OpenHisiIpCam/camera-debug-facility/board/hlk-76x8x/module.jpg

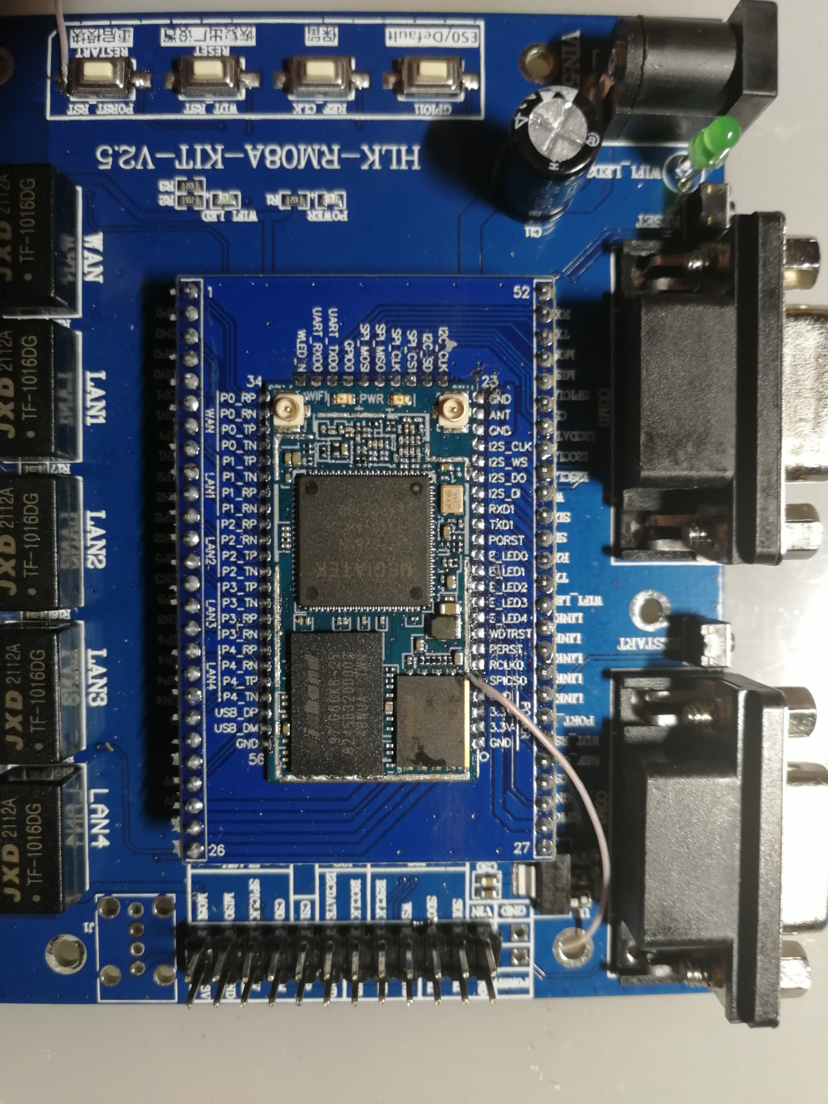
board/hlk-76x8x/module.jpg
