OpenHisiIpCam/camera-debug-facility/board/js7688/drawing.jpg

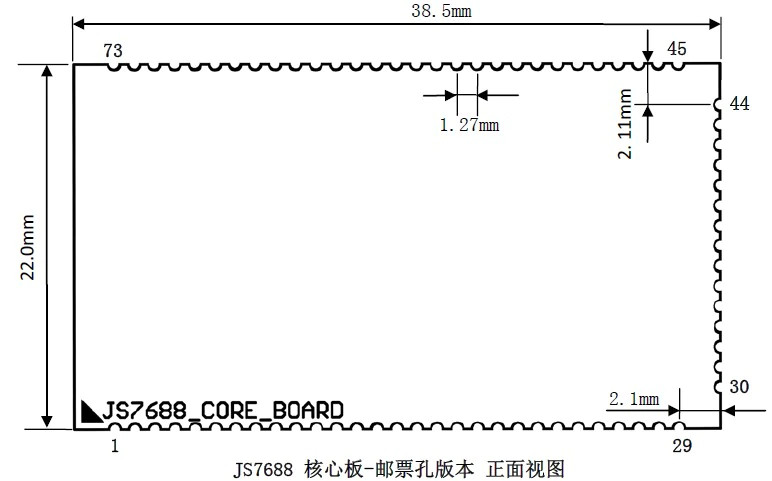
board/js7688/drawing.jpg
