OpenHisiIpCam/camera-debug-facility/board/js7688/js7688.jpg

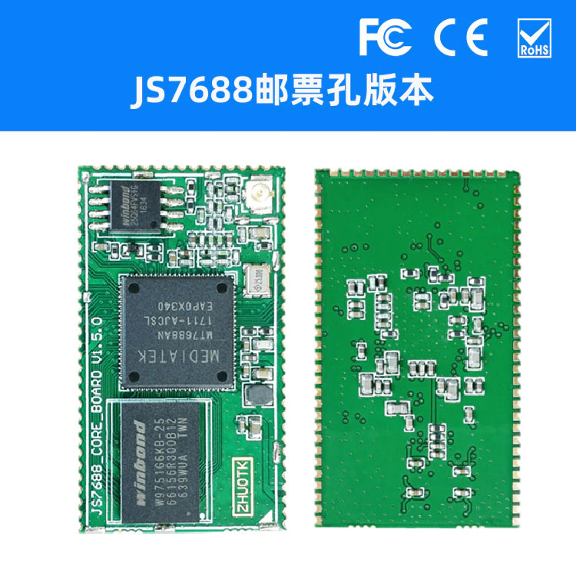
board/js7688/js7688.jpg
