OpenHisiIpCam/camera-debug-facility/hardware/cdf-1/cdf-1-front.jpg

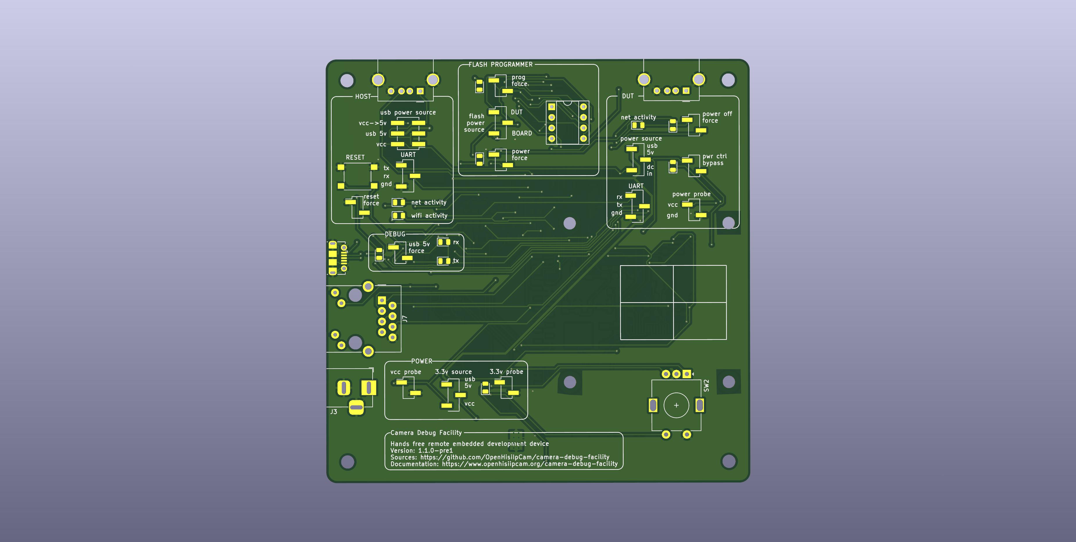
hardware/cdf-1/cdf-1-front.jpg
