OpenHisiIpCam/camera-debug-facility/hardware/references/ssd1306.png

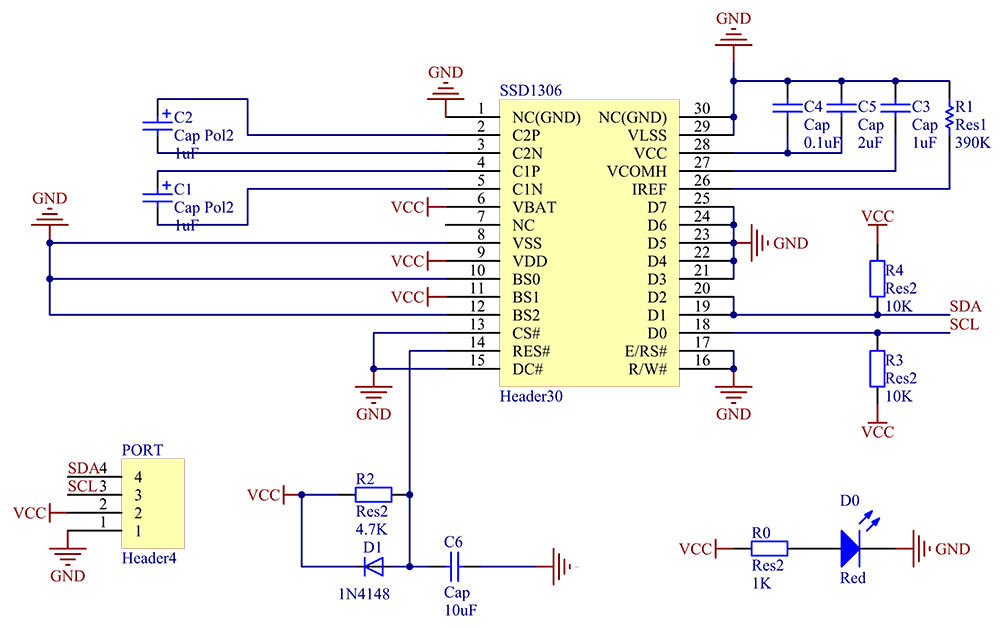
hardware/references/ssd1306.png
