OpenHisiIpCam/camera-debug-facility/board/skw92/skw92a-schematics.pdf

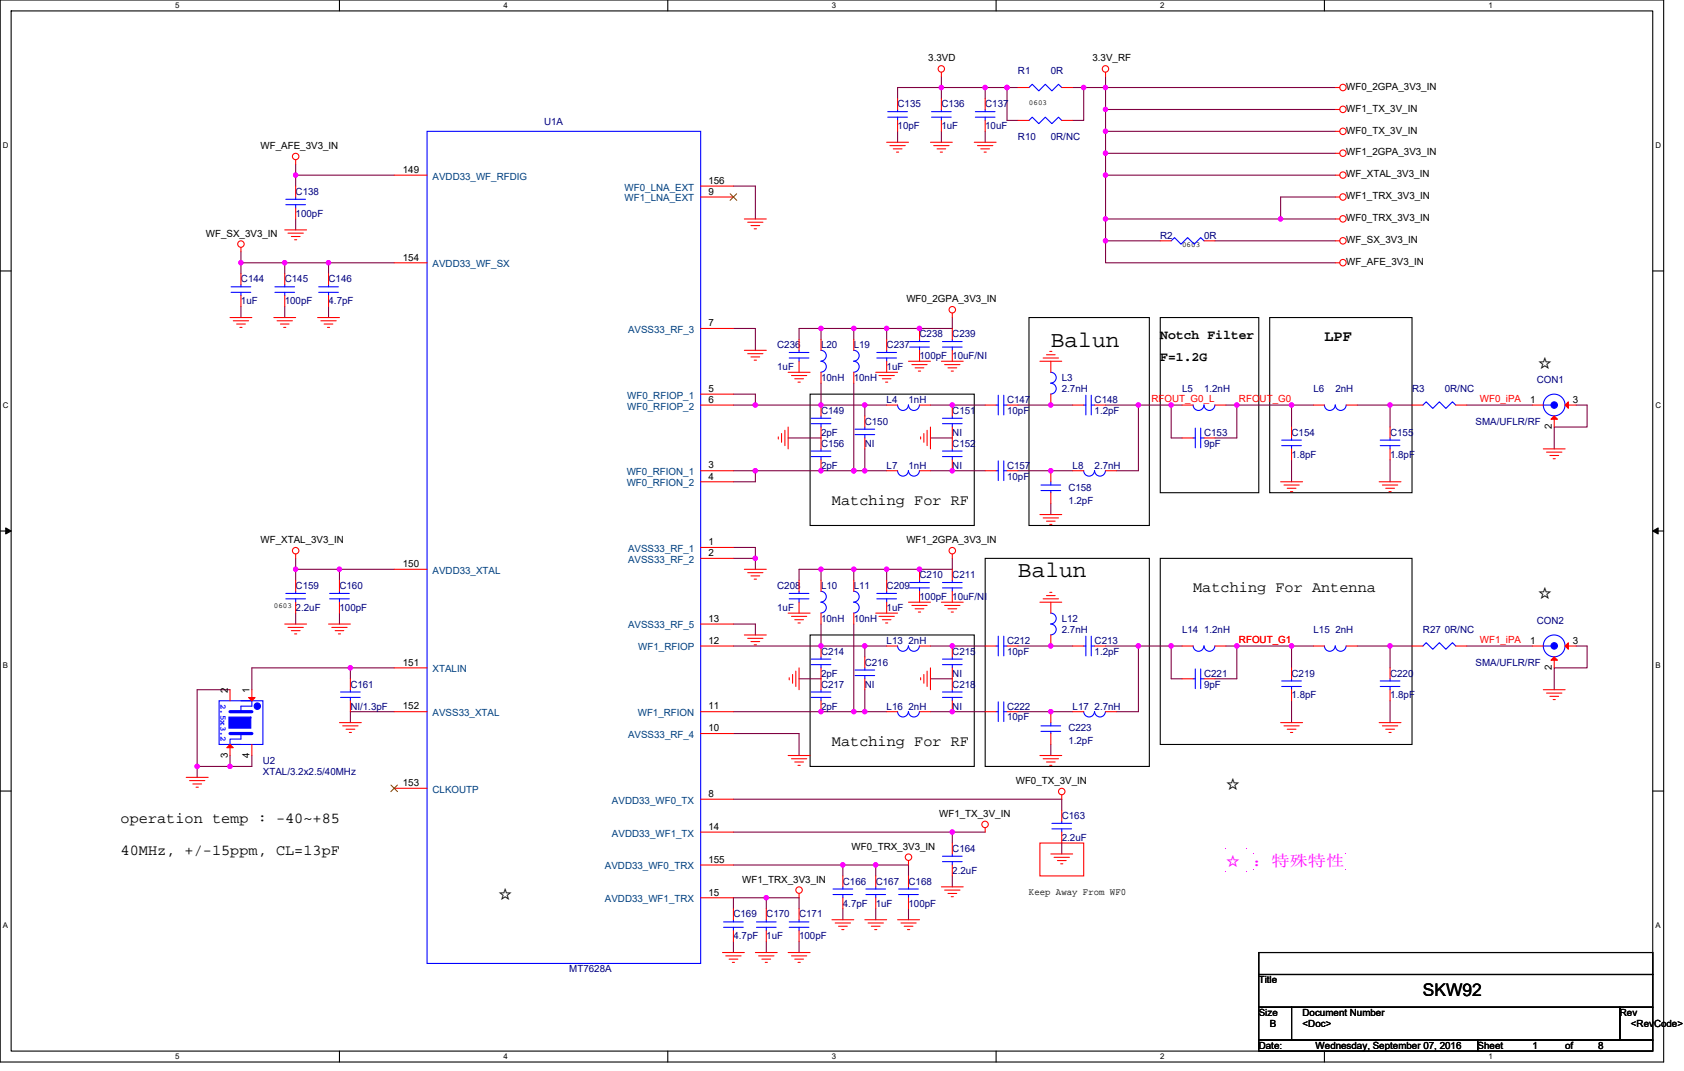
[picture p67: page 1]

CLKOUTP 153 | C223

Matching For RF

Size Size Size B B B | Document Number Document Number Document Number | Rev Rev Rev

Date: Date: Date: Wednesday, September 07, 2016 Wednesday, September 07, 2016 Wednesday, September 07, 2016 | Sheet Sheet Sheet 1 1 1 of of of 8 8 8

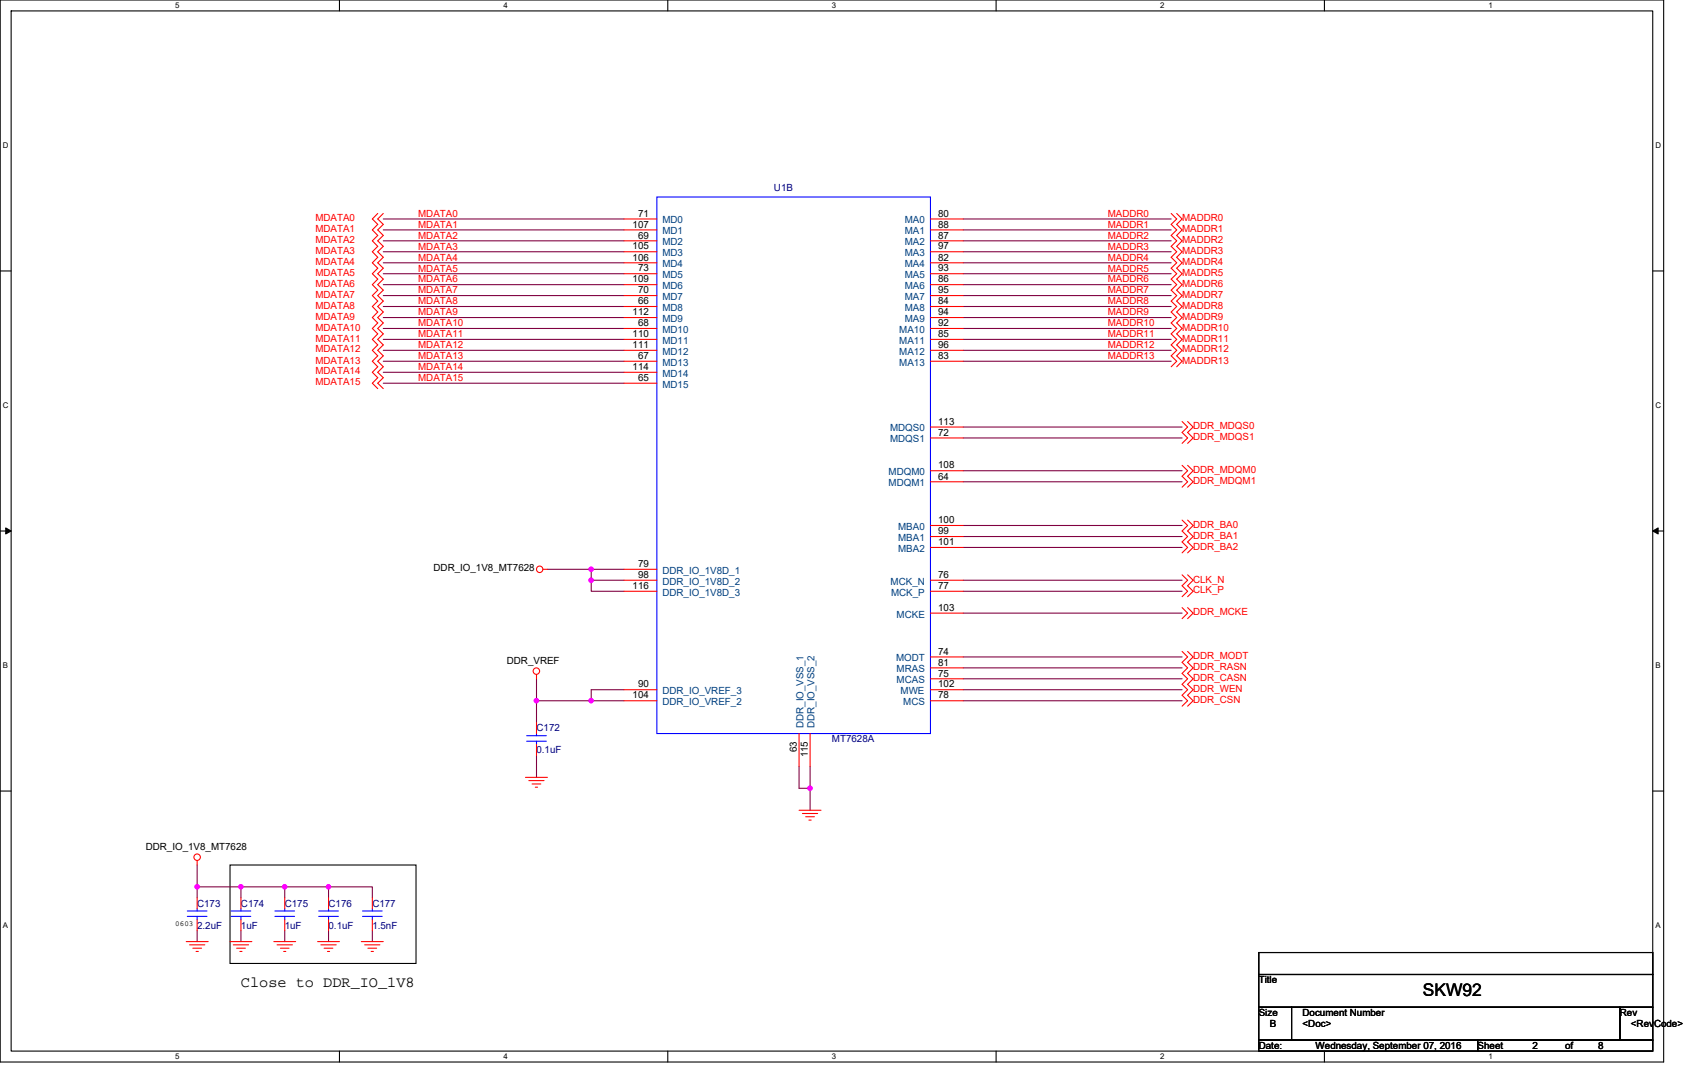
[picture p68: page 2]
Close to DDR_IO_1V8; MADDR0 MADDR1 MADDR2 MADDR3 MADDR4 MADDR5 MADDR6 MADDR7 MADDR8 MADDR9 MADDR10 MADDR11 MADDR12 MADDR13; MDATA0 MDATA1 MDATA2 MDATA3 MDATA4 MDATA5 MDATA6 MDATA7 MDATA8 MDATA9 MDATA10 MDATA11 MDATA12 MDATA13 MDATA14 MDATA15; DDR_IO_1V8_MT7628; DDR_VREF; DDR_MDQS0 DDR_MDQS1; DDR_MDQM0 DDR_MDQM1; DDR_BA0 DDR_BA1 DDR_BA2; CLK_N CLK_P; DDR_MCKE; DDR_MODT DDR_RASN DDR_CASN DDR_WEN DDR_CSN; Title; <Doc>; <RevCode>; SKW92; MDQS0; MDQS1; MDQM0; MDQM1; MBA0; MBA1; MBA2; MCK_N; MCK_P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

Size Size Size B B B | Document Number Document Number Document Number | Rev Rev Rev

Date: Date: Date: Wednesday, September 07, 2016 Wednesday, September 07, 2016 Wednesday, September 07, 2016 | Sheet Sheet Sheet 2 2 2 of of of 8 8 8

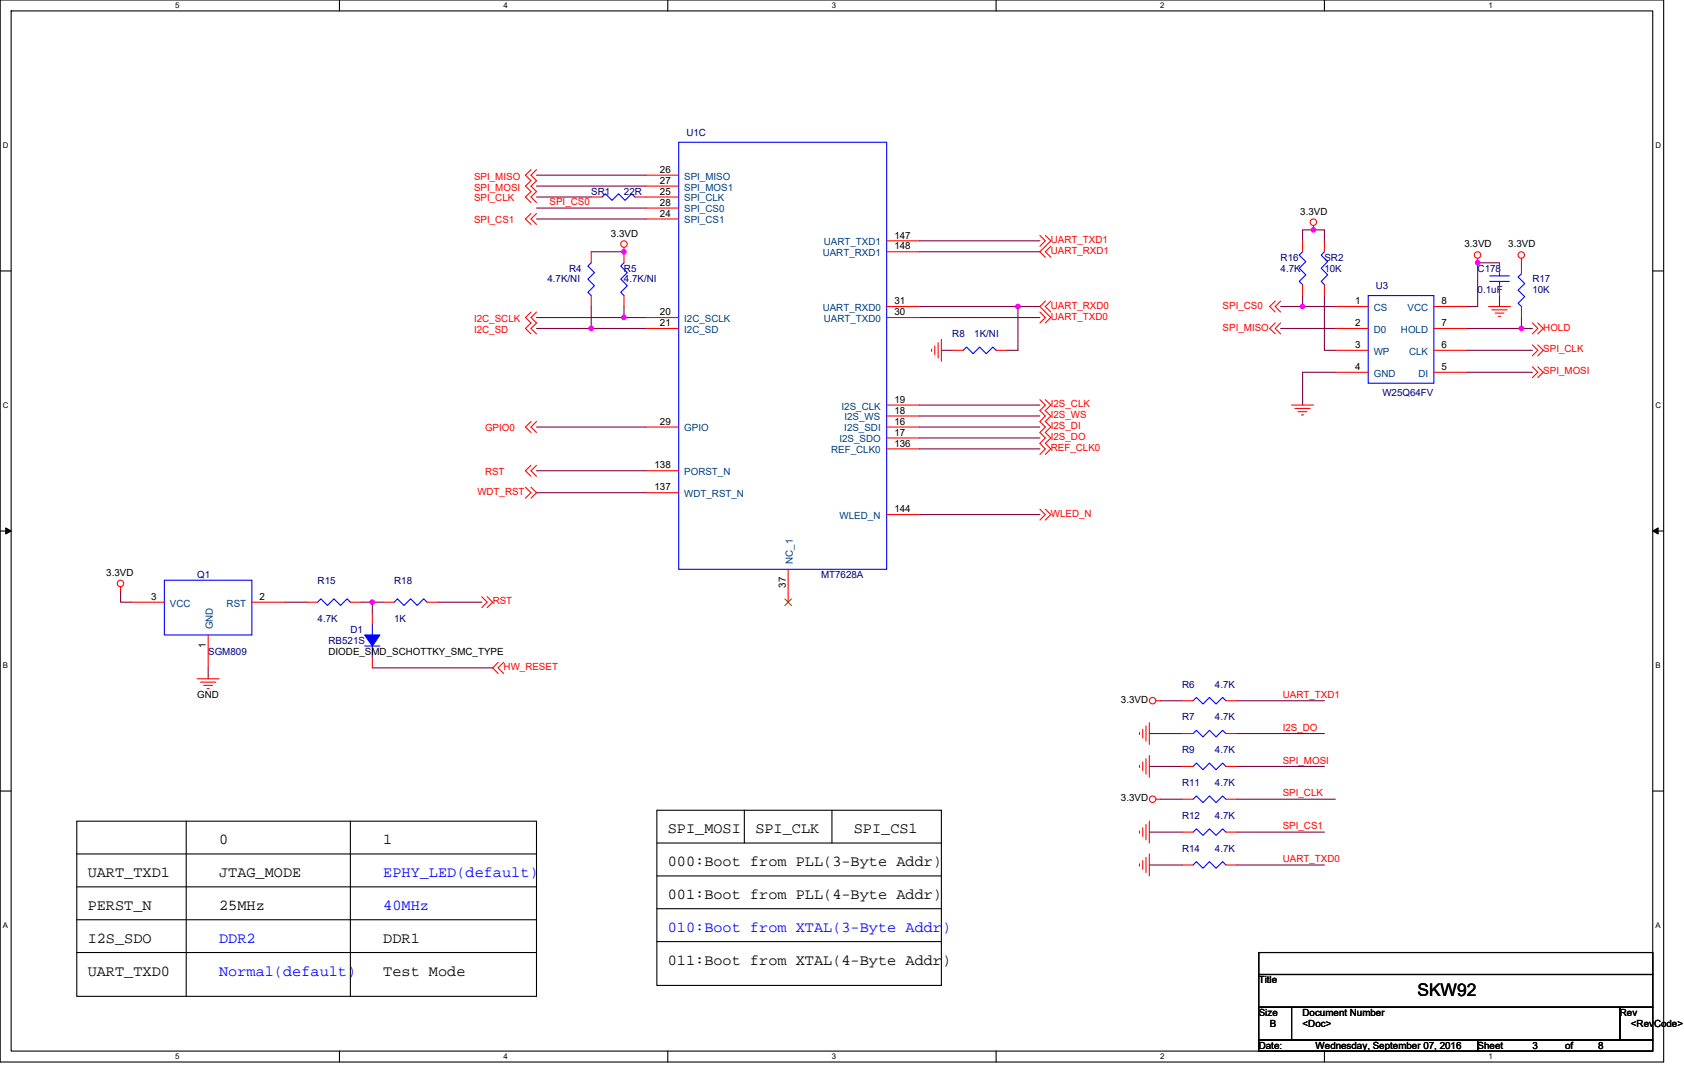
[picture p69: page 3]

000:Boot from PLL(3-Byte Addr)

UART_TXD1 | JTAG_MODE | EPHY_LED(default)

001:Boot from PLL(4-Byte Addr)

PERST_N | 25MHz | 40MHz

010:Boot from XTAL(3-Byte Addr)

I2S_SDO | DDR2 | DDR1

011:Boot from XTAL(4-Byte Addr)

UART_TXD0 | | Test Mode Normal(default)

Size Size Size B B B | Document Number Document Number Document Number | Rev Rev Rev

Date: Date: Date: Wednesday, September 07, 2016 Wednesday, September 07, 2016 Wednesday, September 07, 2016 | Sheet Sheet Sheet 3 3 3 of of of 8 8 8

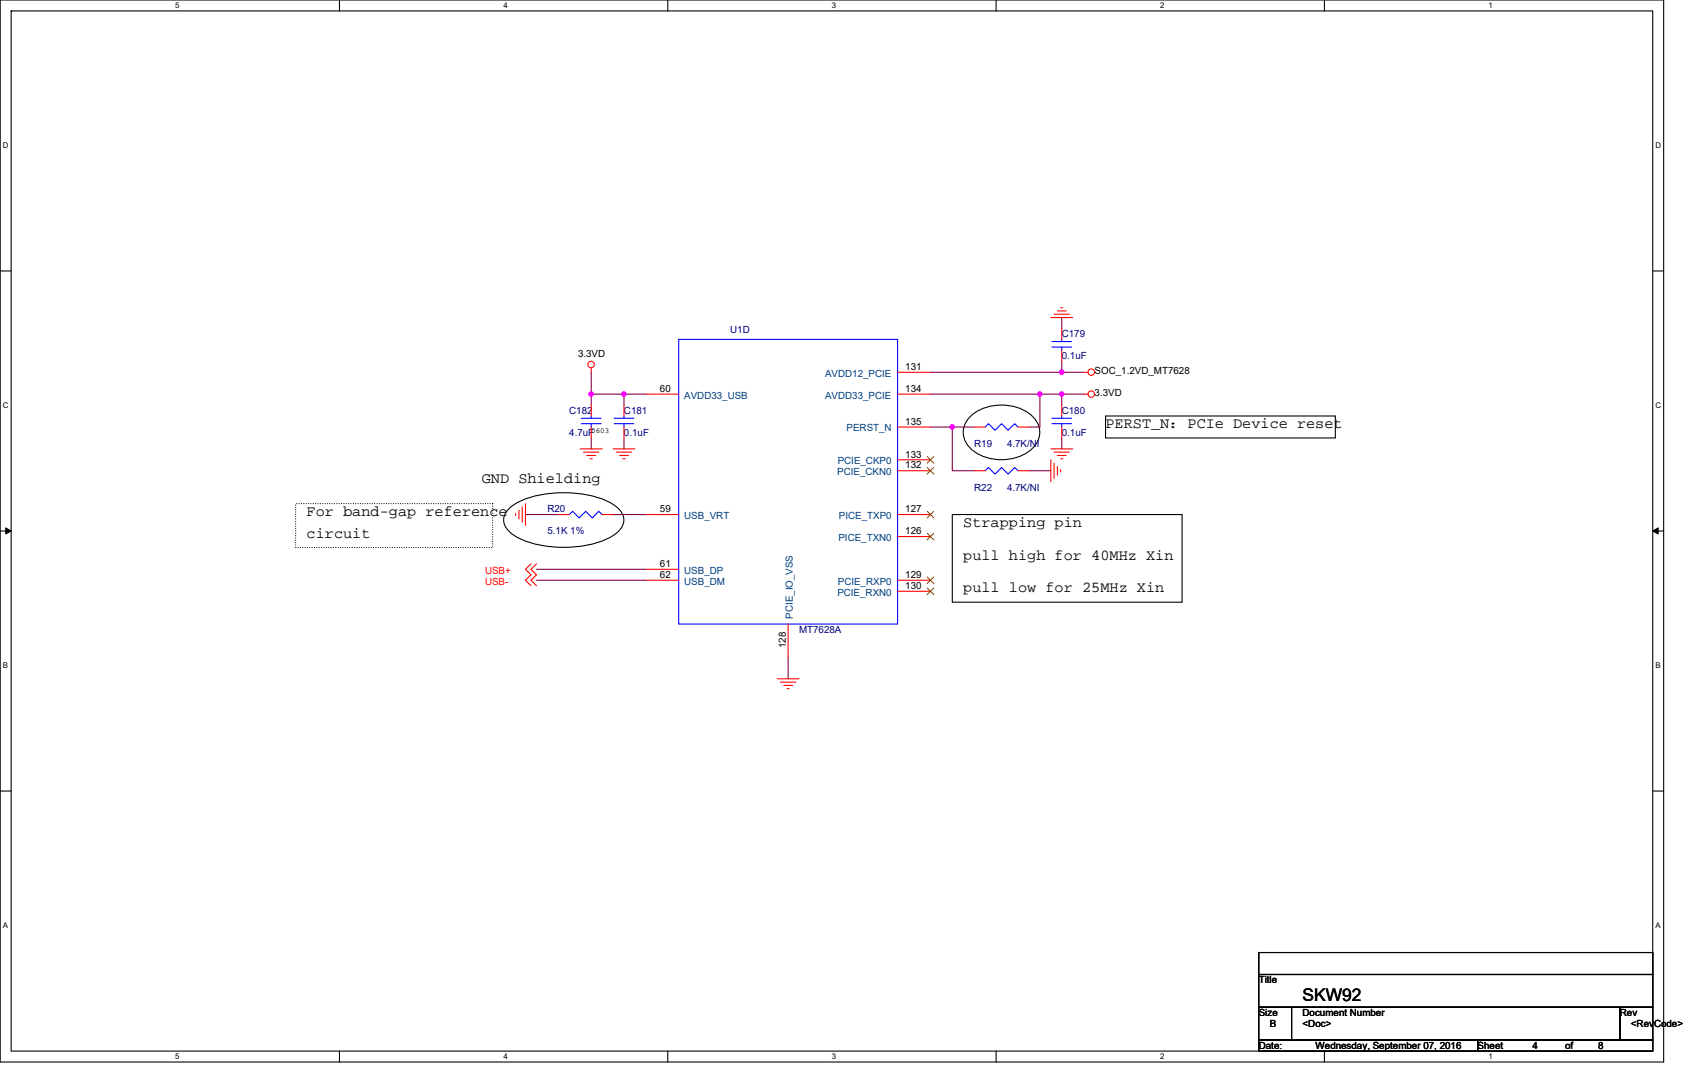
[picture p70: page 4]

For band-gap reference
circuit

pull high for 40MHz Xin

pull low for 25MHz Xin

Size Size Size B B B | Document Number Document Number Document Number | Rev Rev Rev

Date: Date: Date: Wednesday, September 07, 2016 Wednesday, September 07, 2016 Wednesday, September 07, 2016 | Sheet Sheet Sheet 4 4 4 of of of 8 8 8

## Close to MT7628A

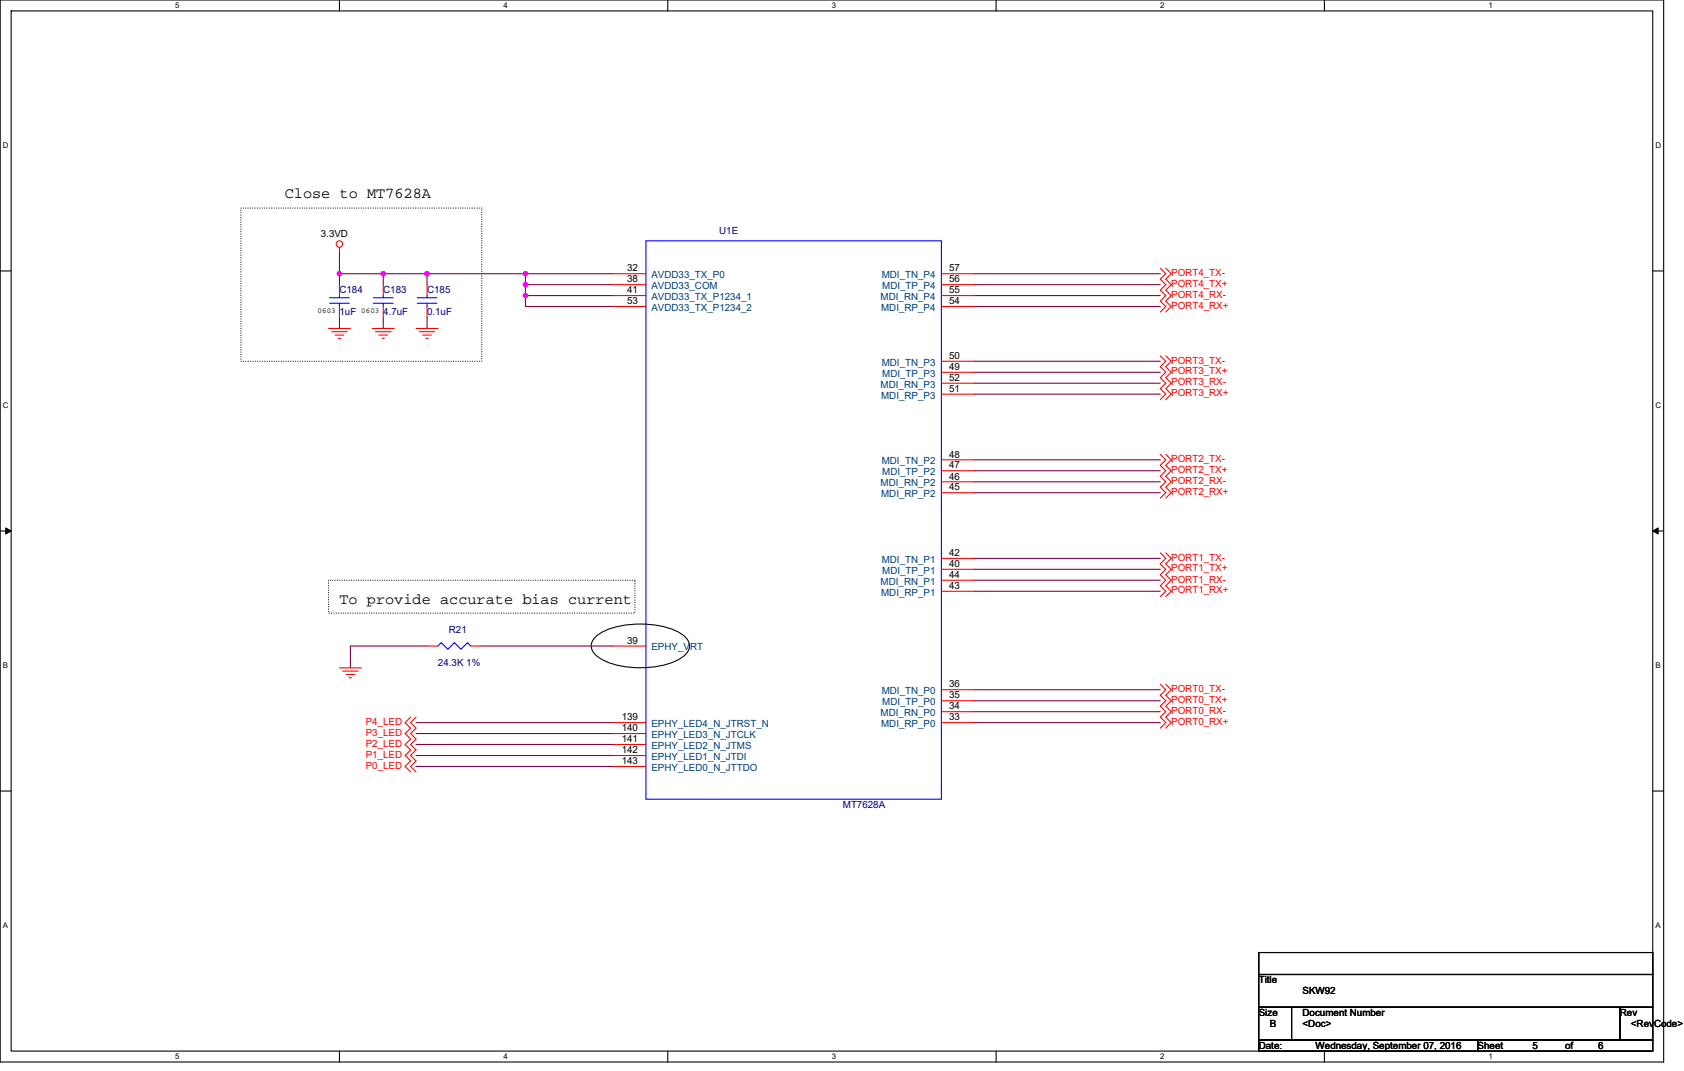
[picture p71: page 5]
PORT0_RX+; PORT0_RX-; PORT0_TX- PORT0_TX+; P4_LED P3_LED P2_LED P1_LED; PORT1_RX+; PORT1_RX-; PORT1_TX- PORT1_TX+; PORT2_RX+; PORT2_RX-; PORT2_TX- PORT2_TX+; PORT3_RX+; PORT3_RX-; PORT3_TX- PORT3_TX+; PORT4_RX+; PORT4_RX-; PORT4_TX- PORT4_TX+; P0_LED; Title; <Doc>; <RevCode>; SKW92; MDI_TN_P4; MDI_TP_P4; MDI_RN_P4; MDI_RP_P4; MDI_TN_P3; MDI_TP_P3; MDI_RN_P3; MDI_RP_P3; MDI_TN_P2; MDI_TP_P2; MDI_RN_P2; MDI_RP_P2; MDI_TN_P1; MDI_TP_P1; MDI_RN_P1; MDI_RP_P1; MDI_TN_P0; MDI_TP_P0; MDI_RN_P0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

To provide accurate bias current

Size Size Size B B B | Document Number Document Number Document Number | Rev Rev Rev

Date: Date: Date: Wednesday, September 07, 2016 Wednesday, September 07, 2016 Wednesday, September 07, 2016 | Sheet Sheet Sheet 5 5 5 of of of 6 6 6

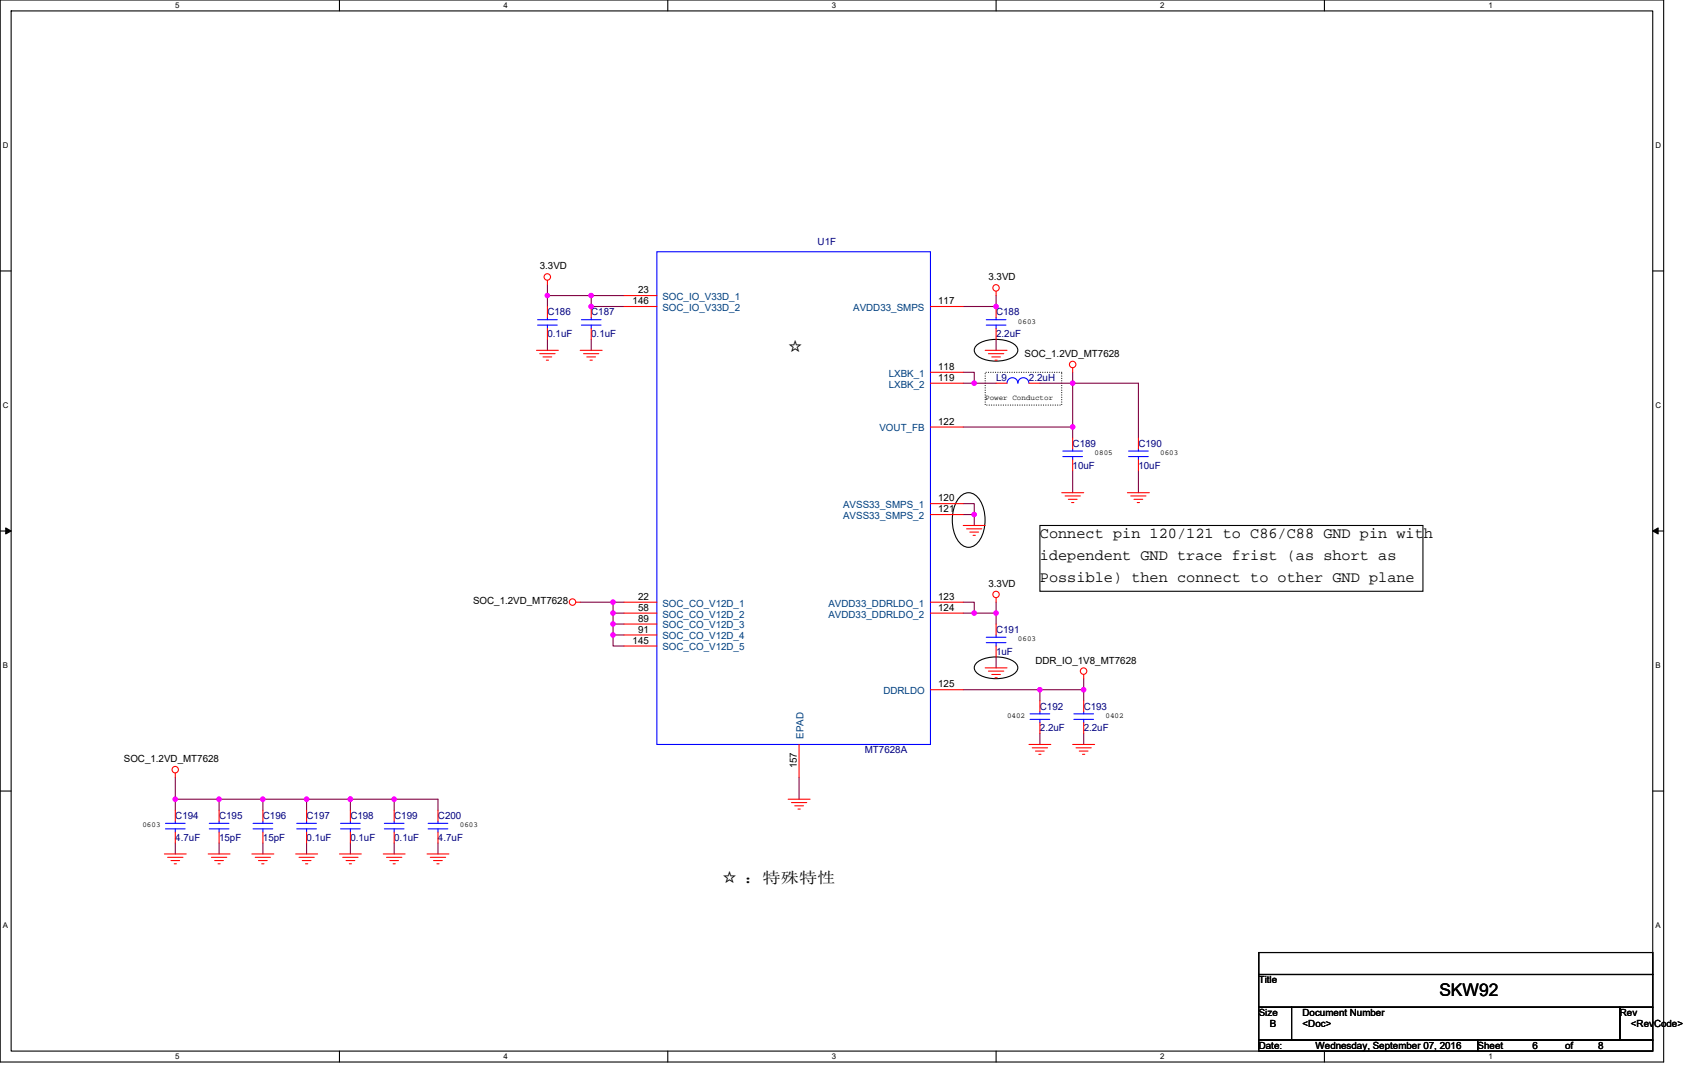
[picture p72: page 6]

Connect pin 120/121 to C86/C88 GND pin with
idependent GND trace frist (as short as
Possible) then connect to other GND plane

Size Size Size B B B | Document Number Document Number Document Number | Rev Rev Rev

Date: Date: Date: Wednesday, September 07, 2016 Wednesday, September 07, 2016 Wednesday, September 07, 2016 | Sheet Sheet Sheet 6 6 6 of of of 8 8 8

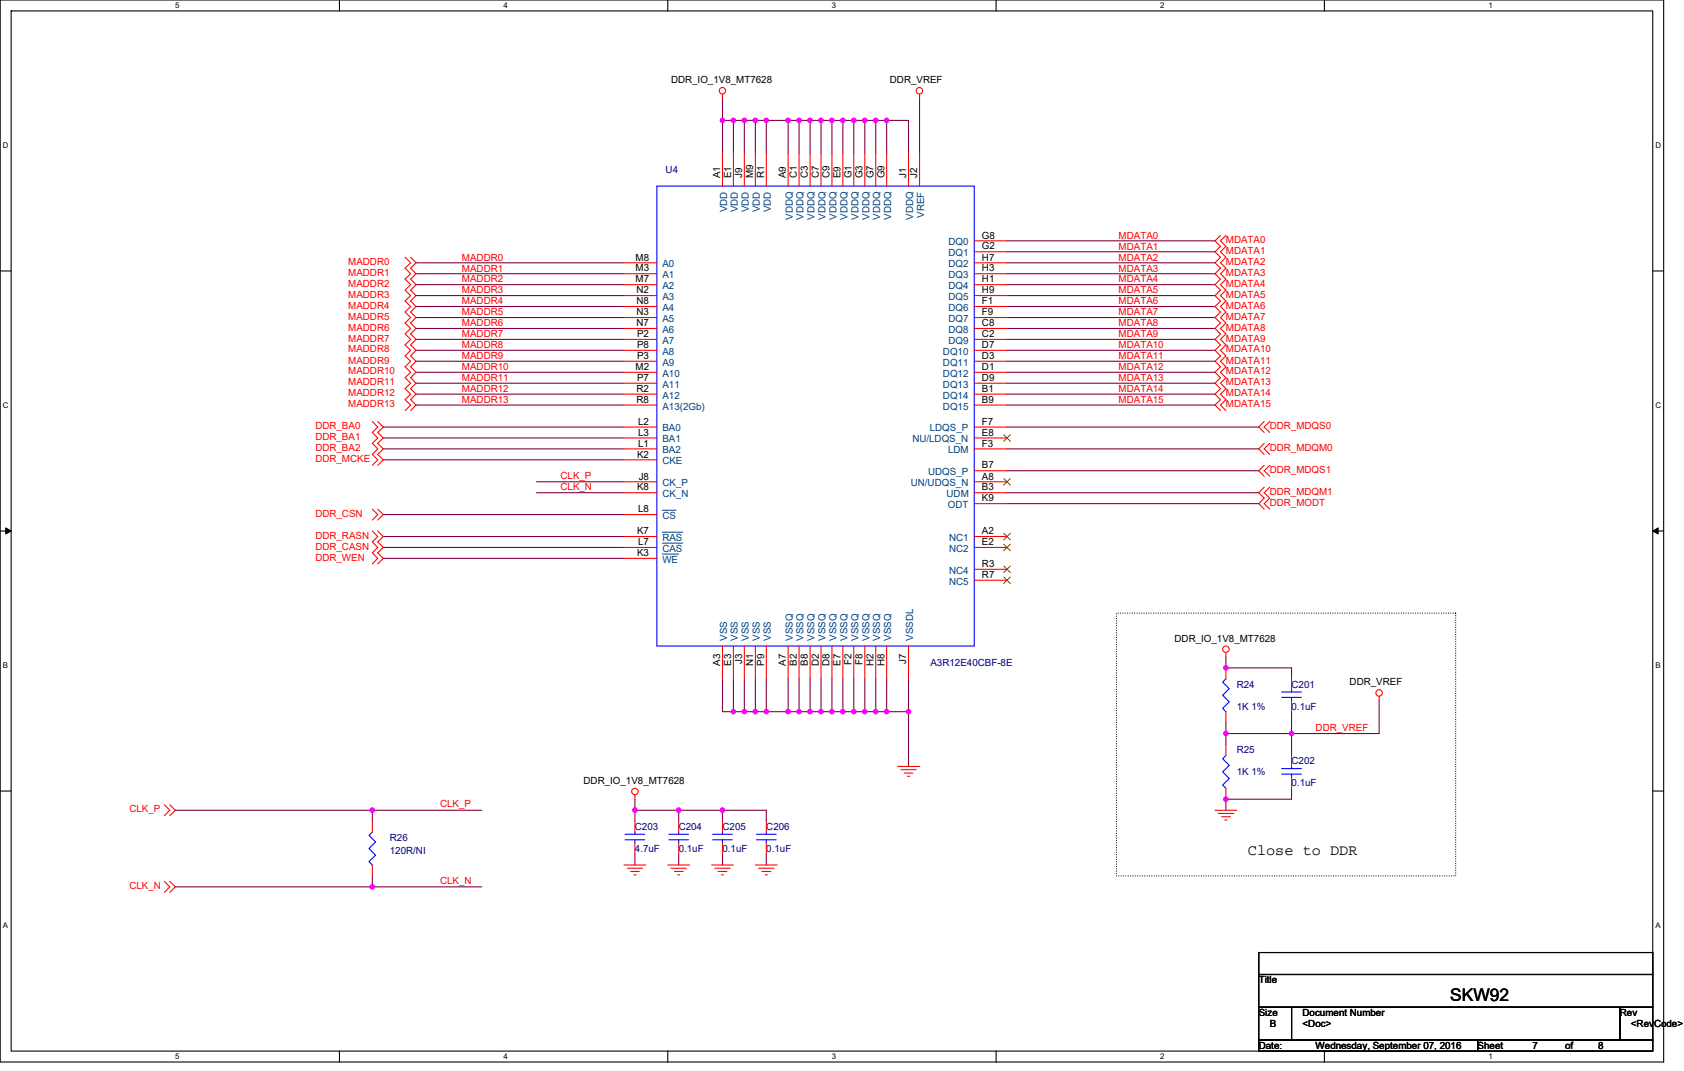
[picture p73: page 7]

Size Size Size B B B | Document Number Document Number Document Number | Rev Rev Rev

Date: Date: Date: Wednesday, September 07, 2016 Wednesday, September 07, 2016 Wednesday, September 07, 2016 | Sheet Sheet Sheet 7 7 7 of of of 8 8 8

## Port3 and port4 multiplexing

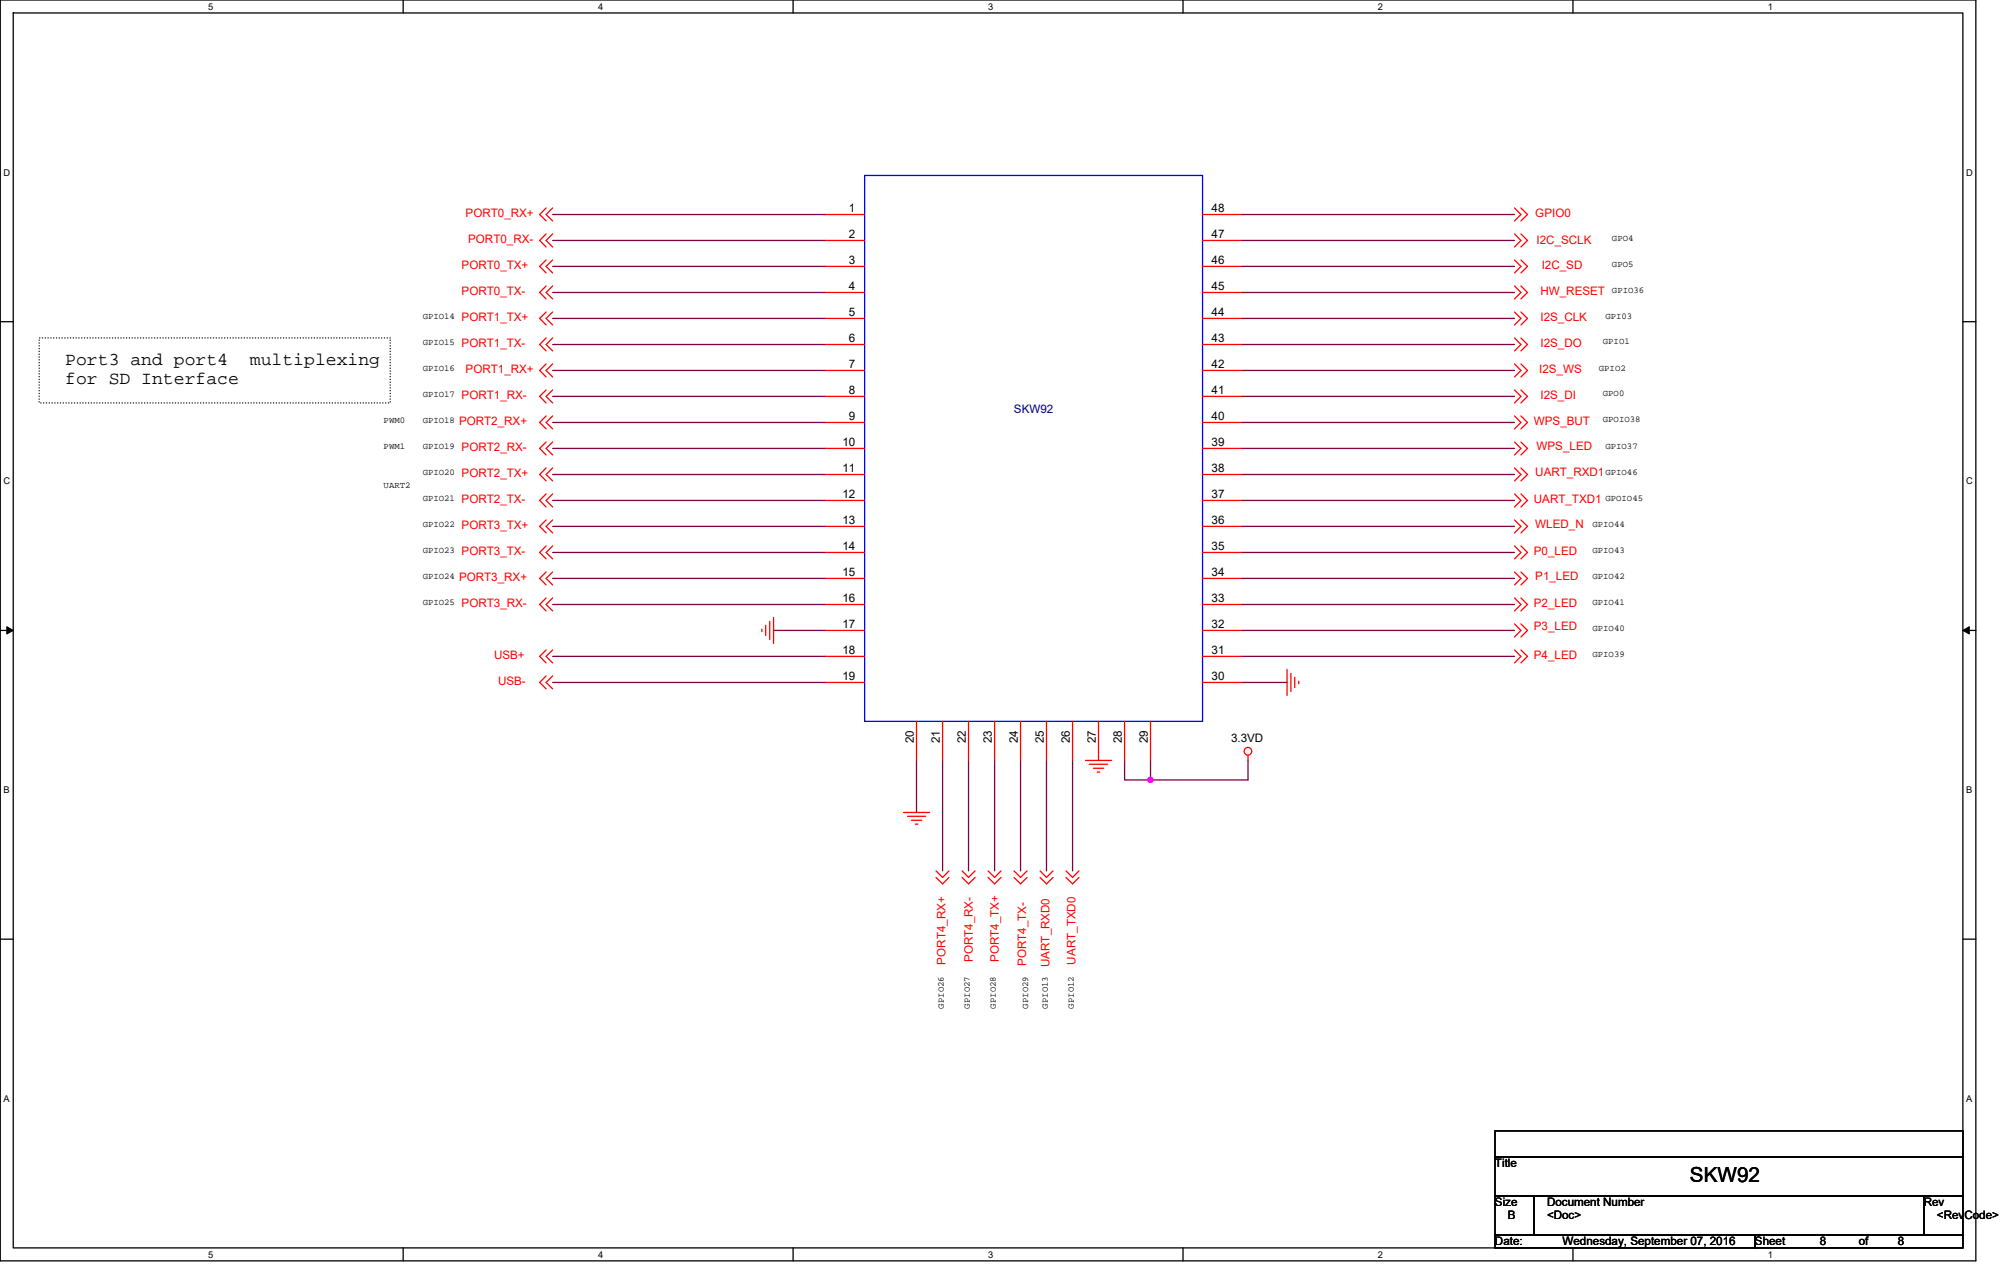
[picture p74: page 8]
PWM1; PWM0; GPI03; GPIO2; GPIO1; GPO0; GPIO13; GPIO12; GPIO21; GPIO22; GPIO23; GPIO24; GPIO25; GPIO18; GPIO17; GPIO16; GPIO15; GPIO14; GPIO20; GPIO19; UART2; GPIO26; GPIO27; GPIO28; GPIO29; GPIO46; GPOIO45; GPIO44; GPIO42; GPIO43; GPO5; GPO4; GPIO37; GPIO41; GPIO40; GPIO39; GPOIO38; GPIO36; PORT1_TX+; PORT1_RX+; PORT1_RX-; PORT1_TX-; PORT2_RX+; PORT2_RX-; PORT2_TX+; PORT2_TX-; PORT3_TX+; PORT3_TX-; PORT3_RX+; PORT3_RX-; PORT0_RX+ PORT0_RX- PORT0_TX+ PORT0_TX-; PORT4_RX+; PORT4_RX-; PORT4_TX+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

for SD Interface

Size Size Size B B B | Document Number Document Number Document Number | Rev Rev Rev

Date: Date: Date: Wednesday, September 07, 2016 Wednesday, September 07, 2016 Wednesday, September 07, 2016 | Sheet Sheet Sheet 8 8 8 of of of 8 8 8
