OpenHisiIpCam/camera-debug-facility/board/js7688/JS76x8_base_board_sch_v1.7.2.pdf

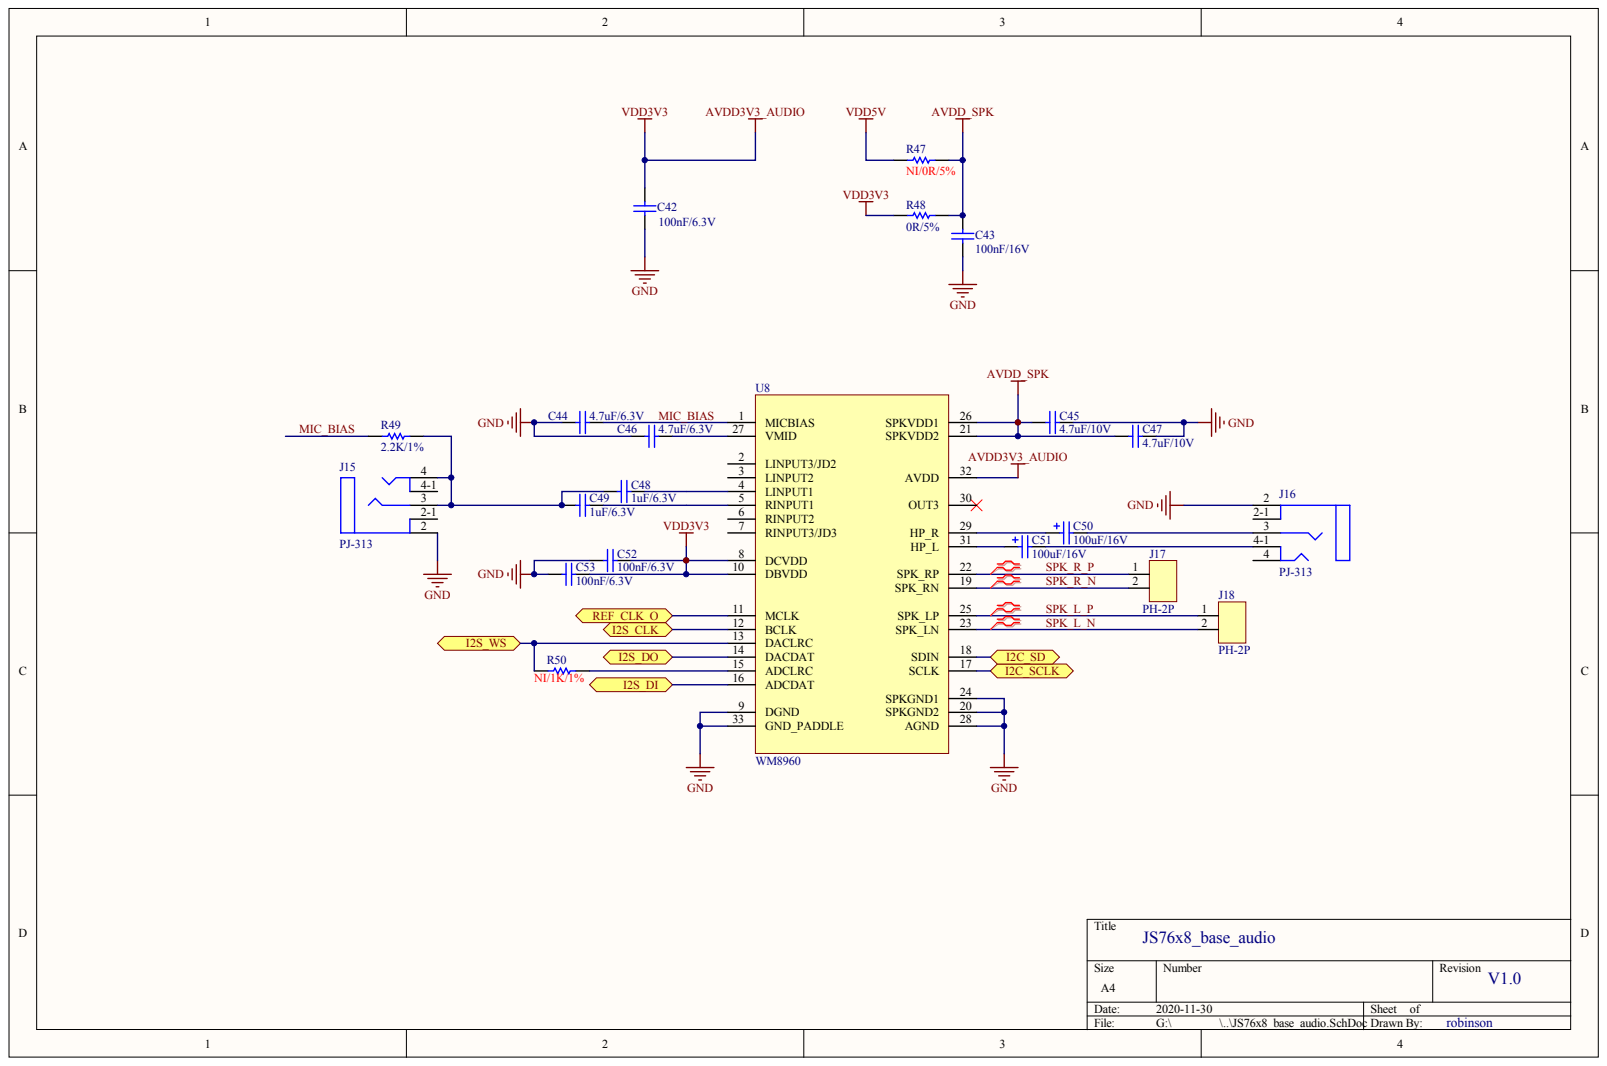
[picture p75: page 1]

VMID 27 | 4.7uF/10V | C47

4 | LINPUT3/JD2 2

C53 | | 100nF/6.3V | DBVDD 10

MCLK 11 BCLK 12 DACLRC 13 | SPK_R_N 2

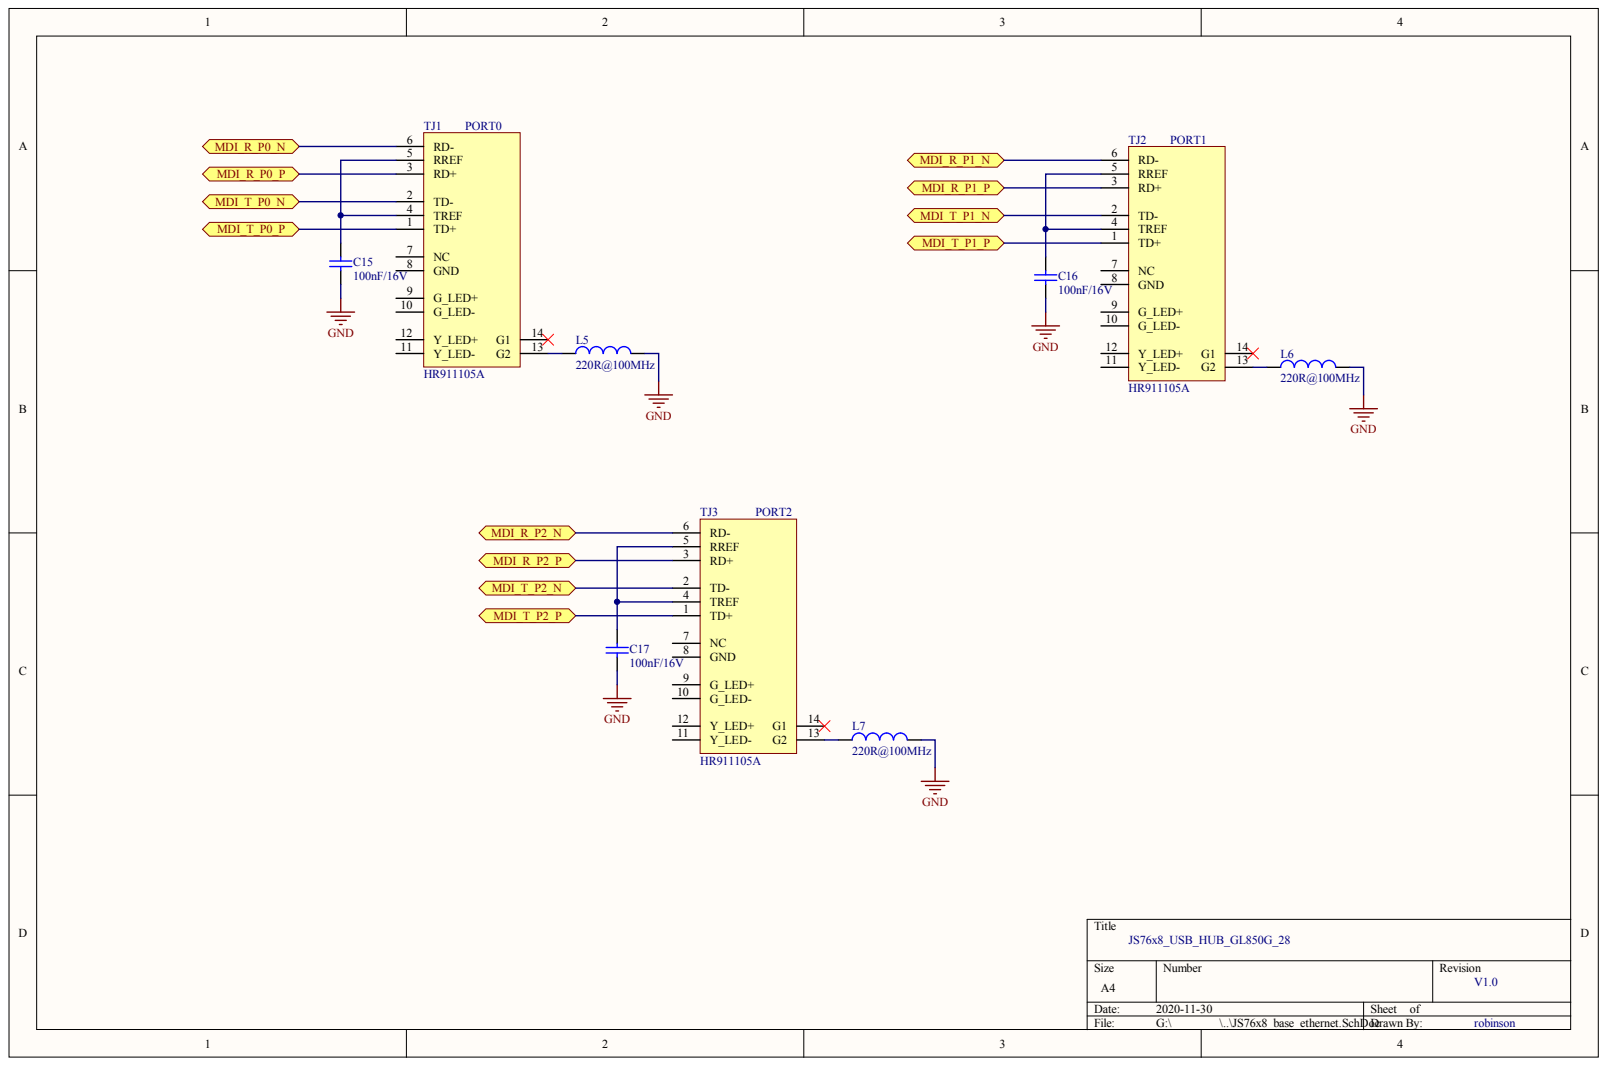
[picture p76: page 2]

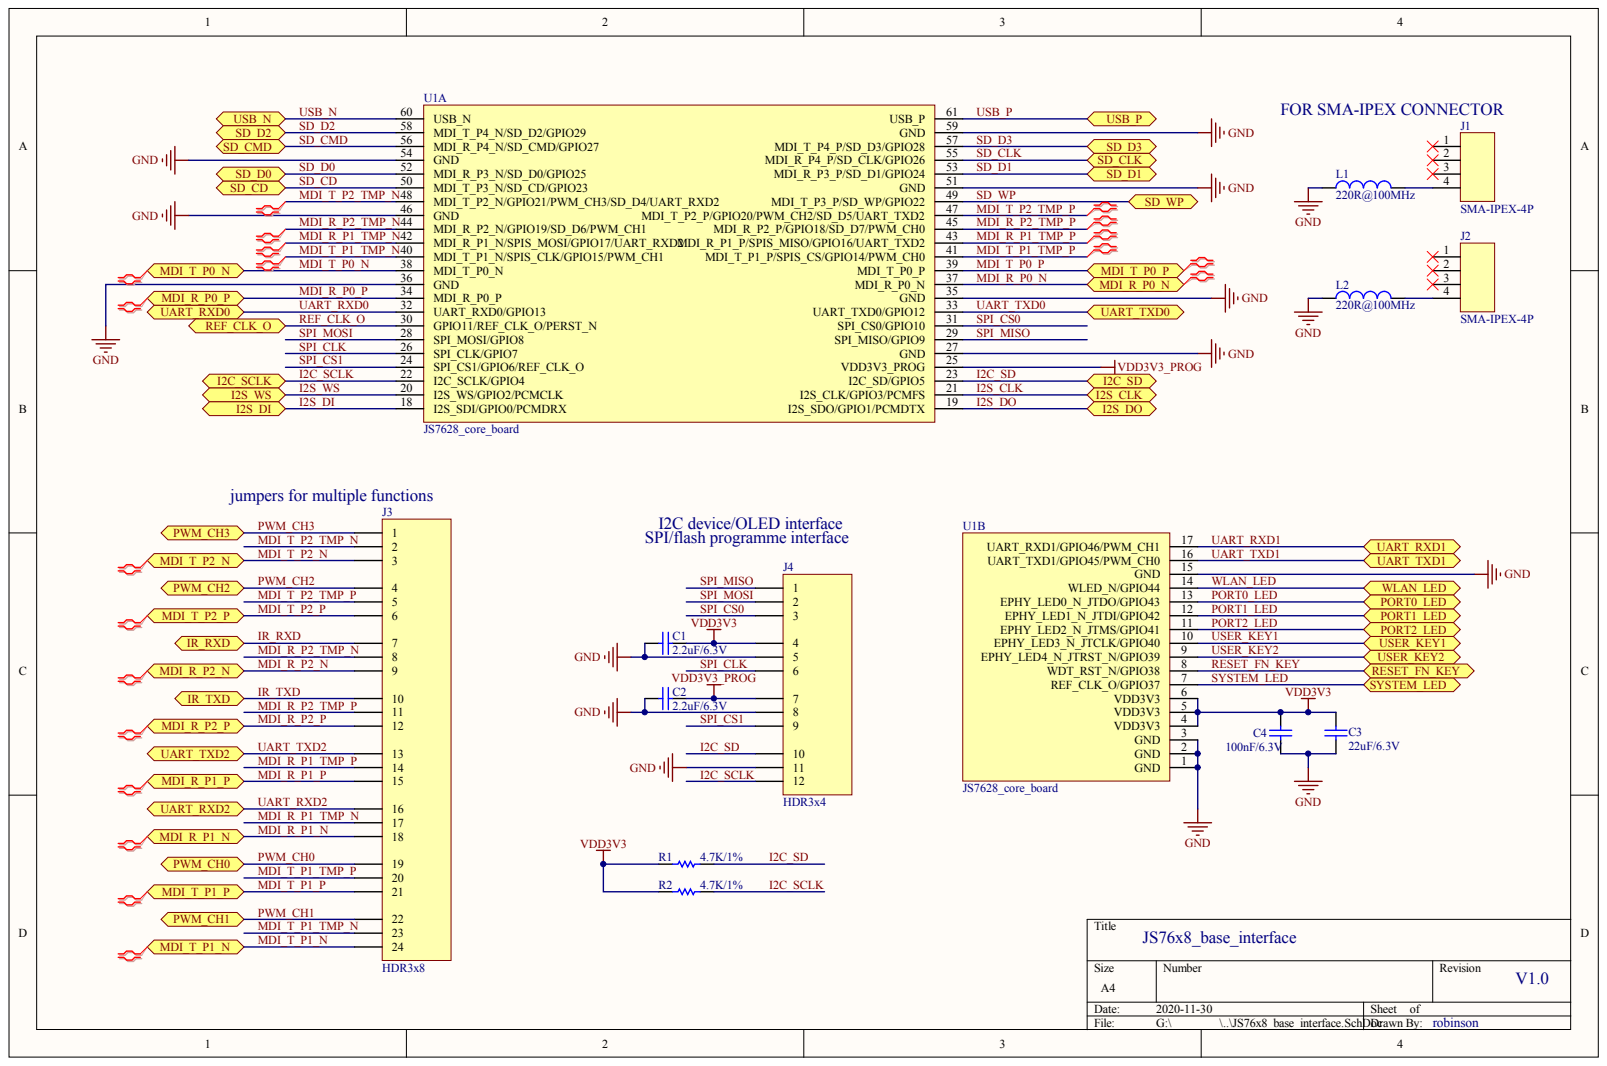
[picture p77: page 3]

DDra oc wn By

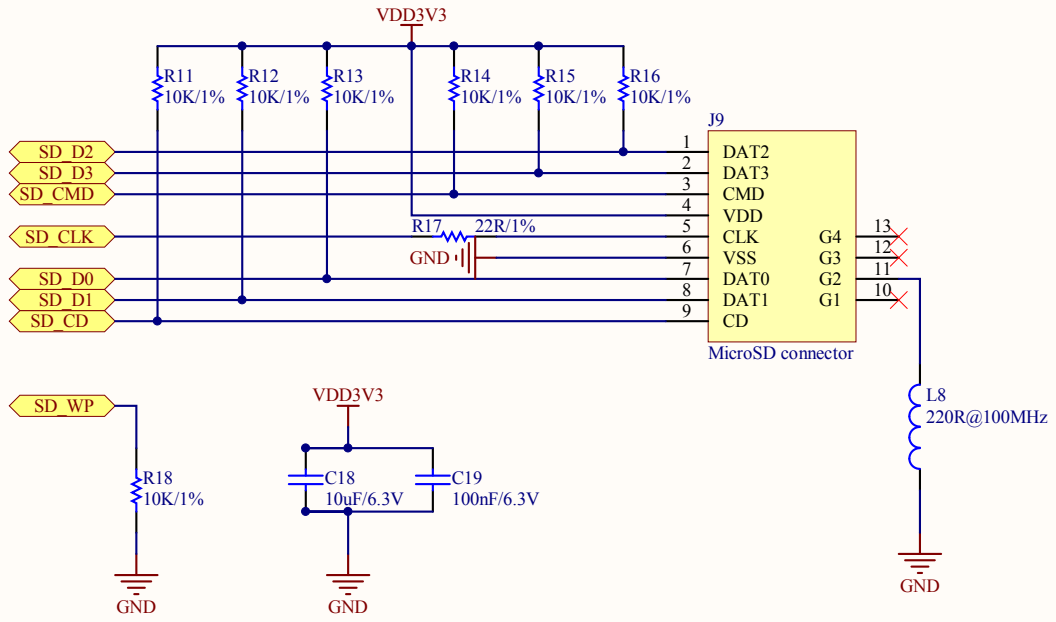
[picture p78: page 4]

chDDra oc wn By

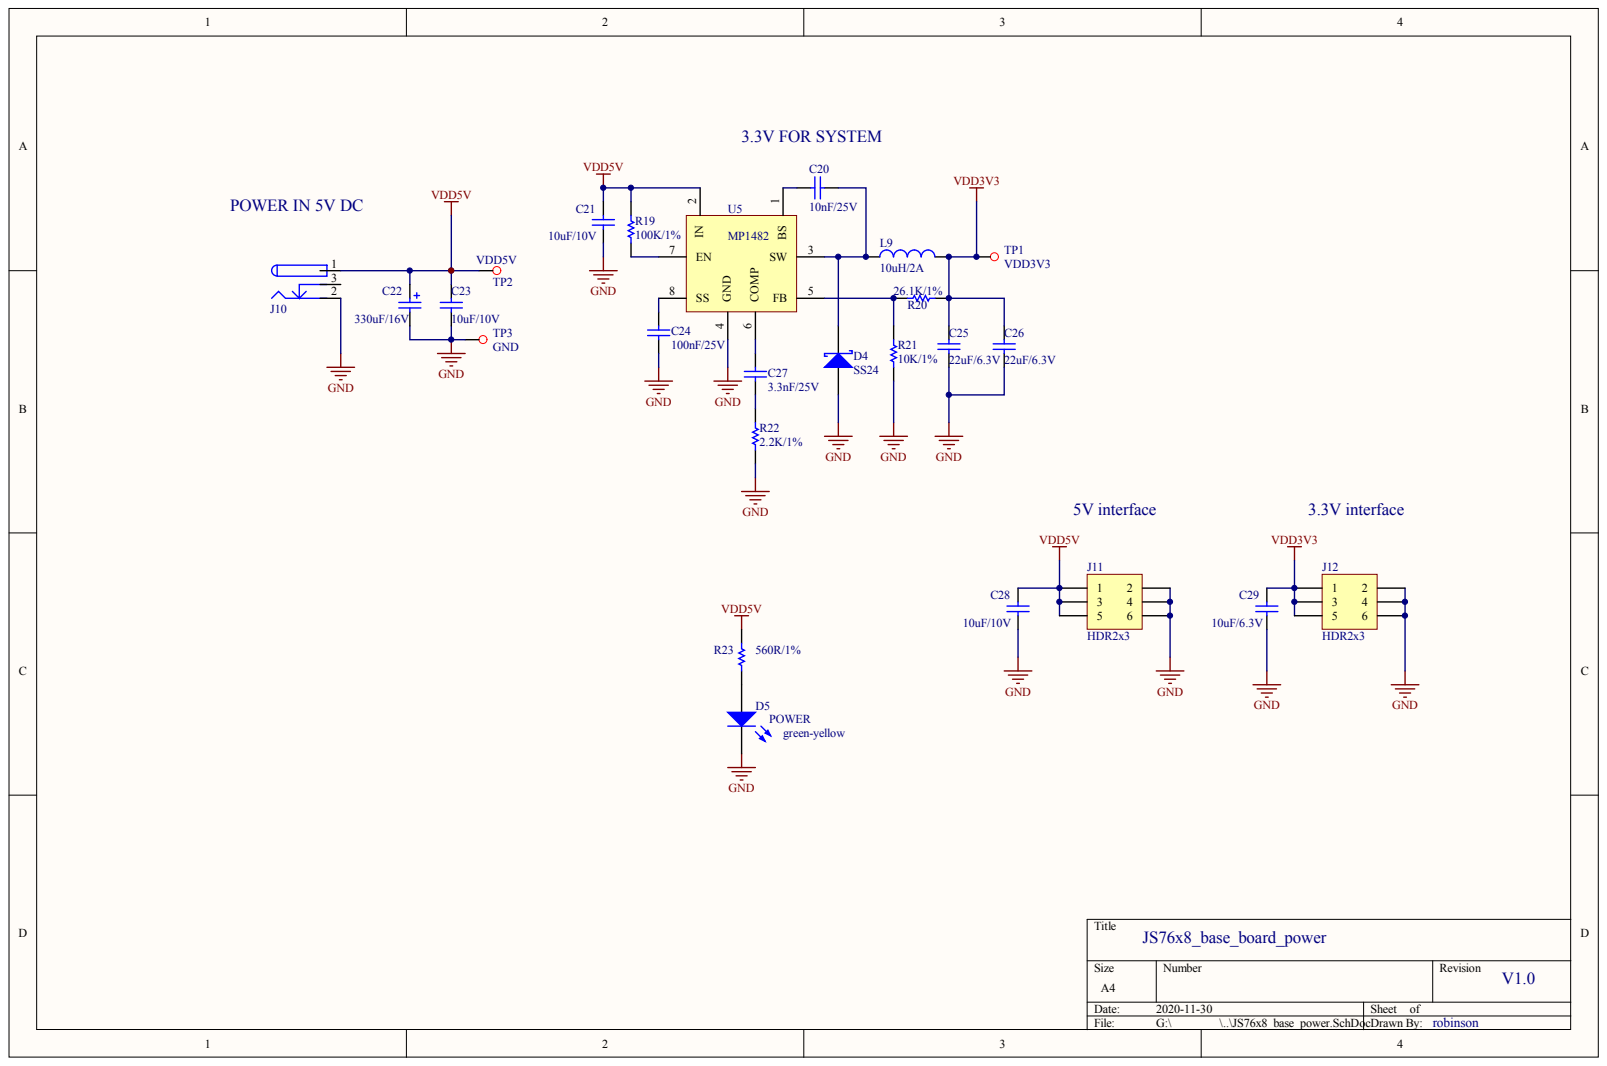
[picture p79: page 5]

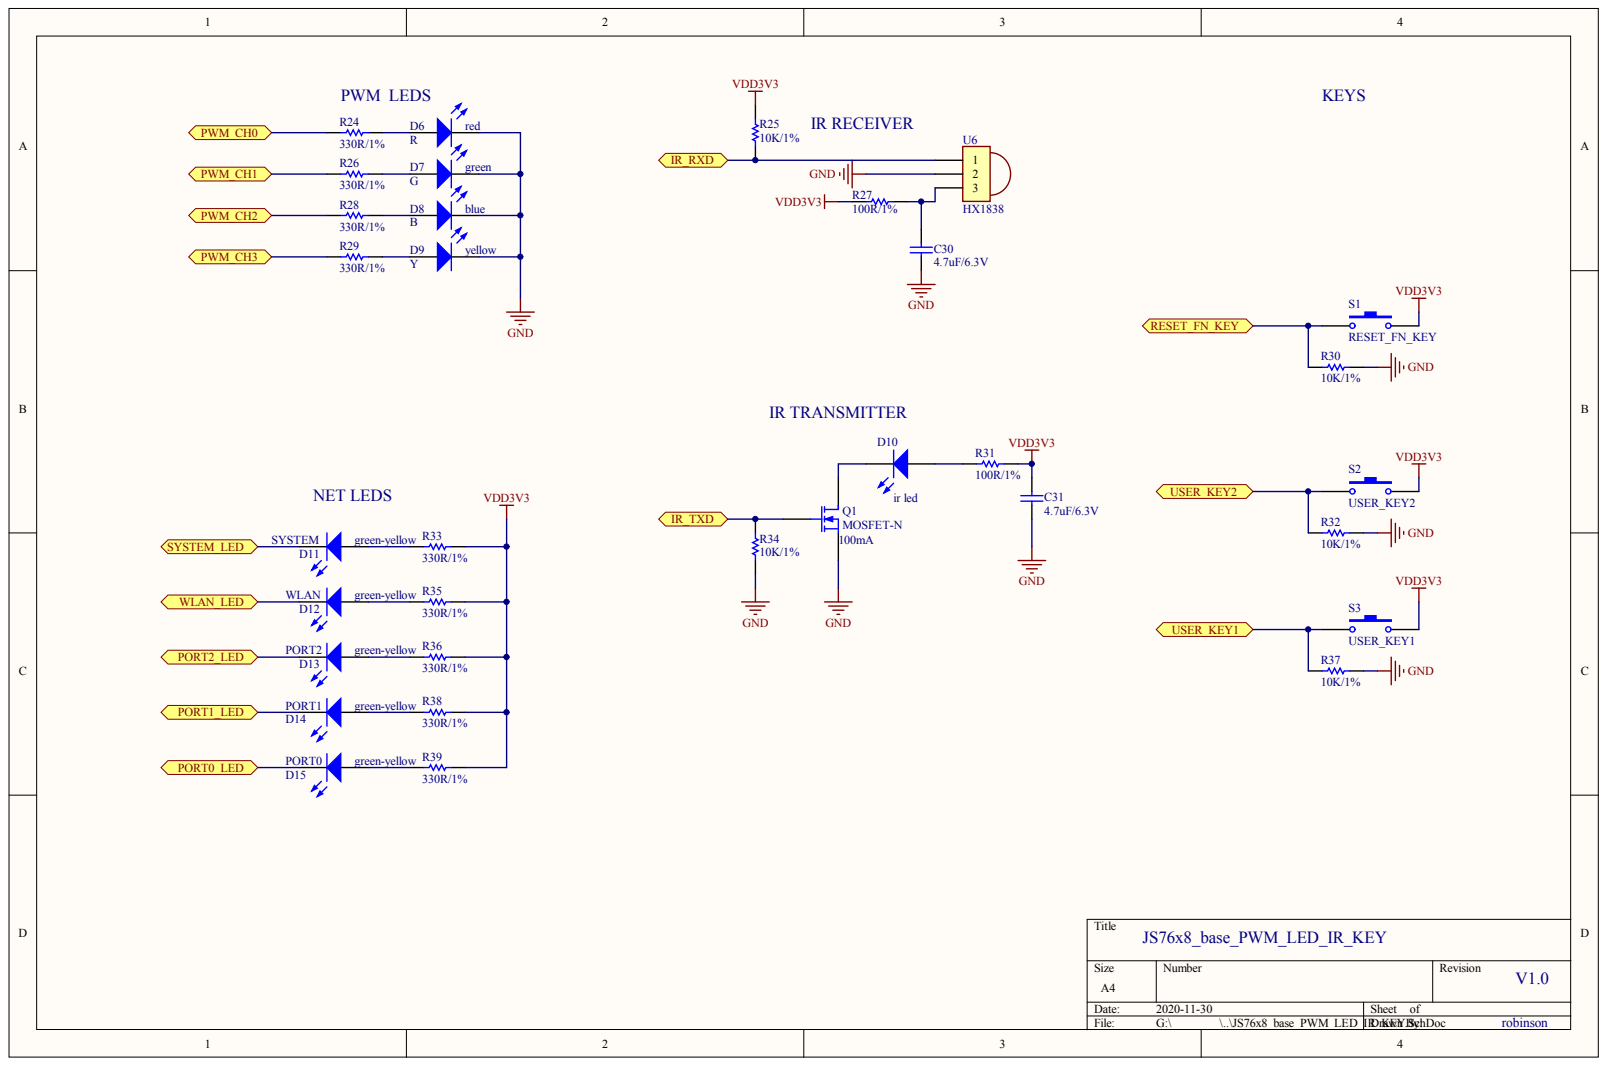
[picture p80: page 6]

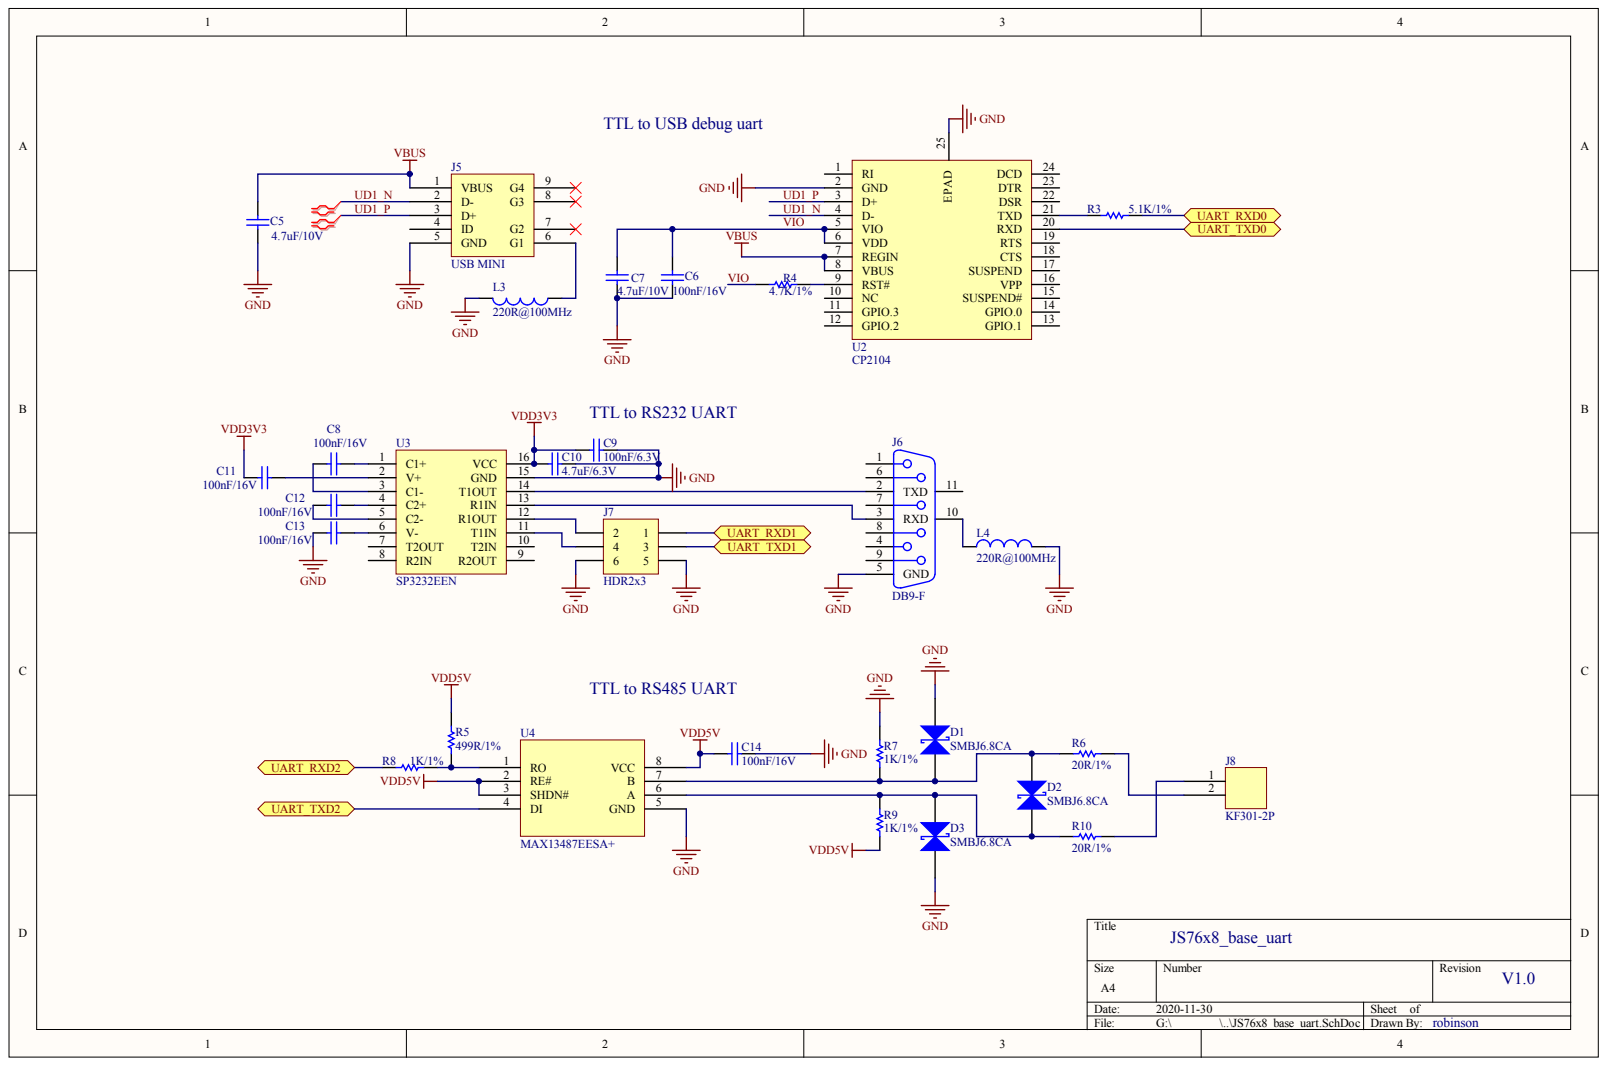
[picture p81: page 7]

TTL to USB debug uart

VBUS | VDD 6

REGIN 7

V+ 2 | 4.7uF/6.3V
C1- 3
C2+ 4 | 7 | RXD 3
C2- 5
V- 6 | | 2 1 4 3 6 5 | 8 4 9

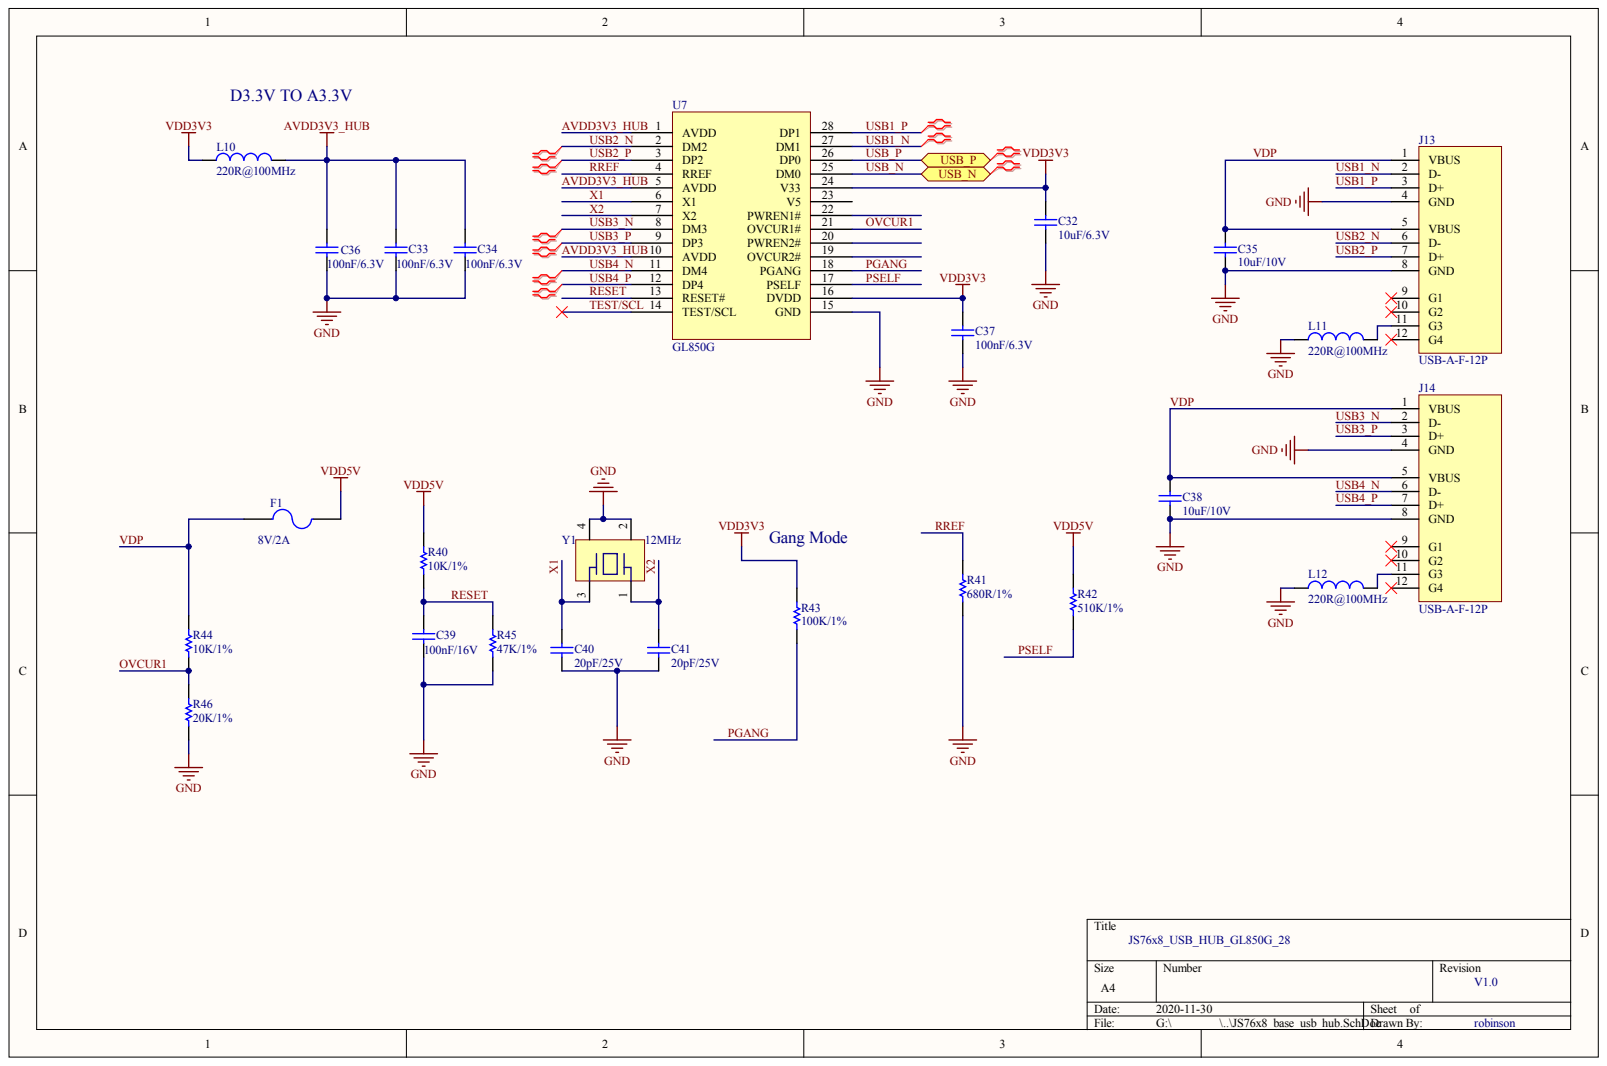
[picture p82: page 8]
