OpenHisiIpCam/camera-debug-facility/board/wms-76x8/WKA-76X8Pro原理图.pdf

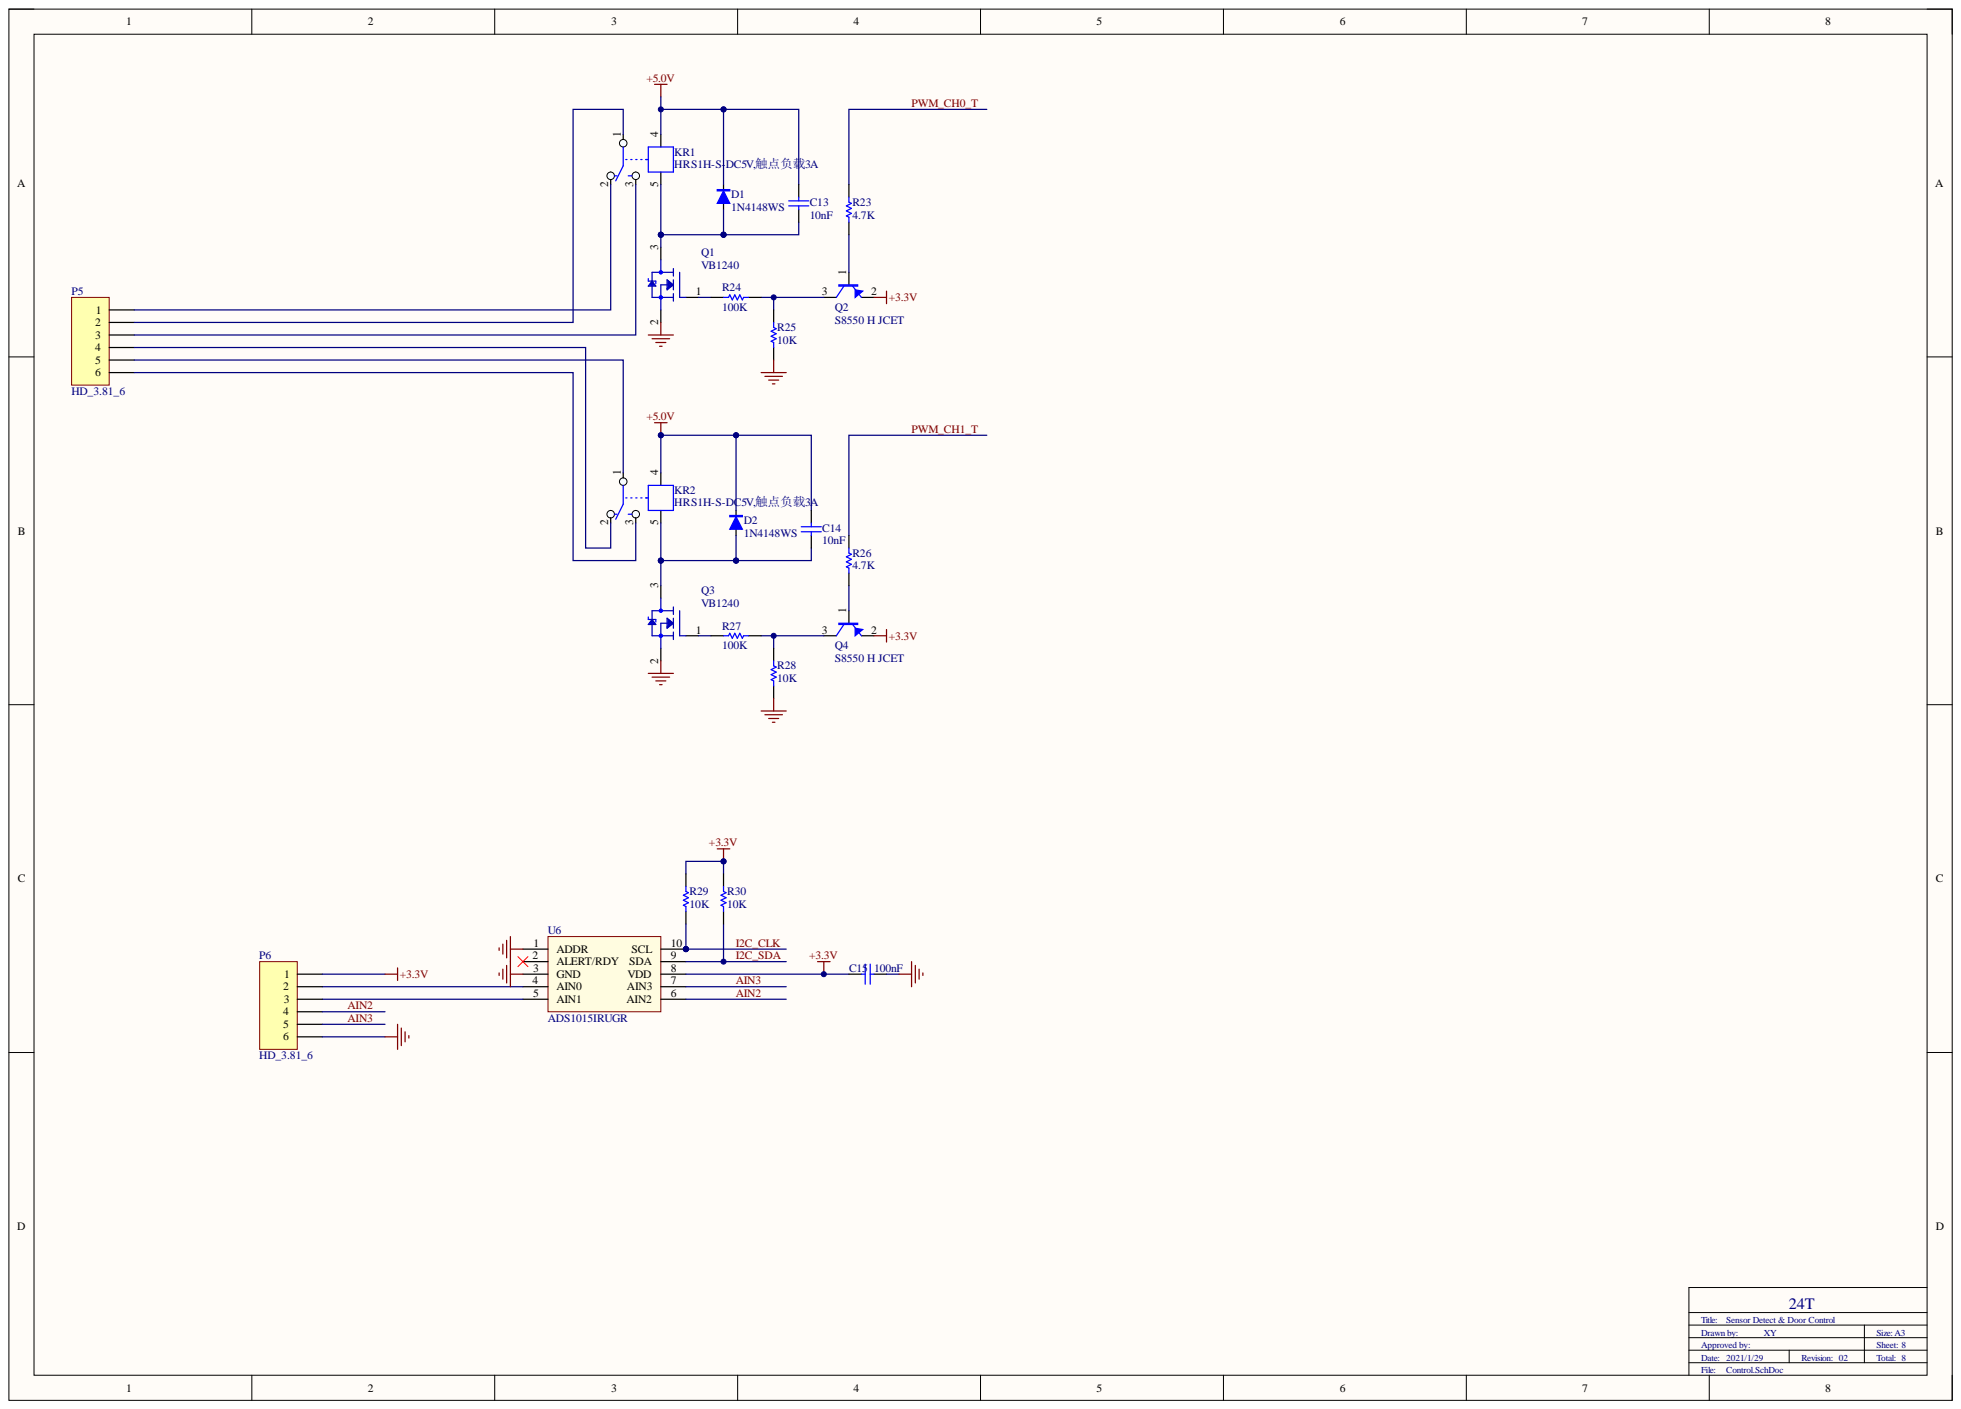
[picture p83: page 1]

sor Detect & Door Control

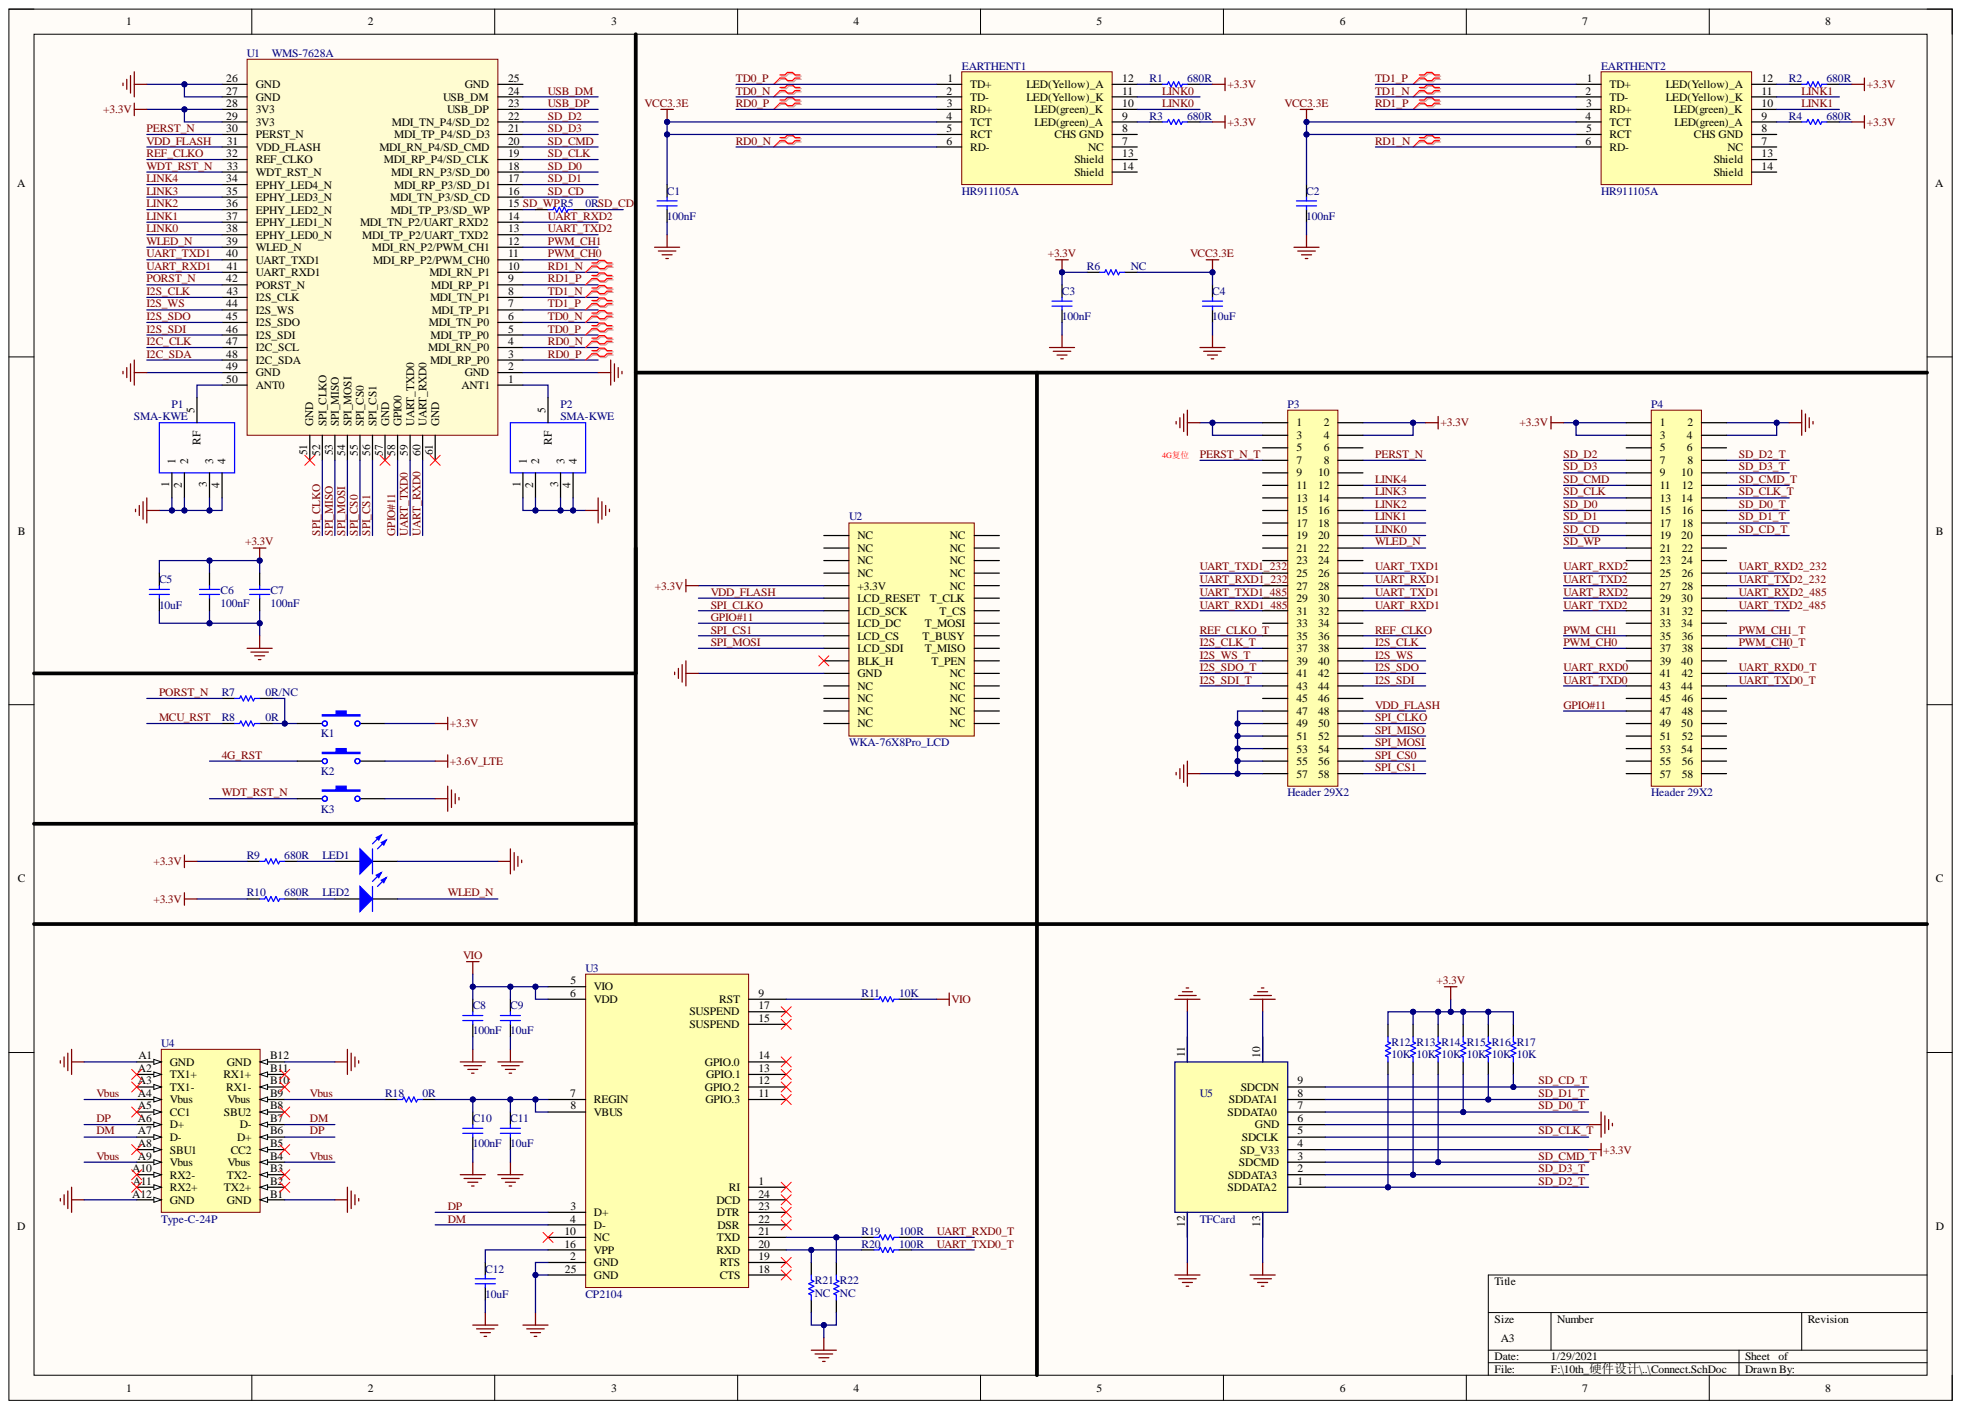
[picture p84: page 2]

GND 2

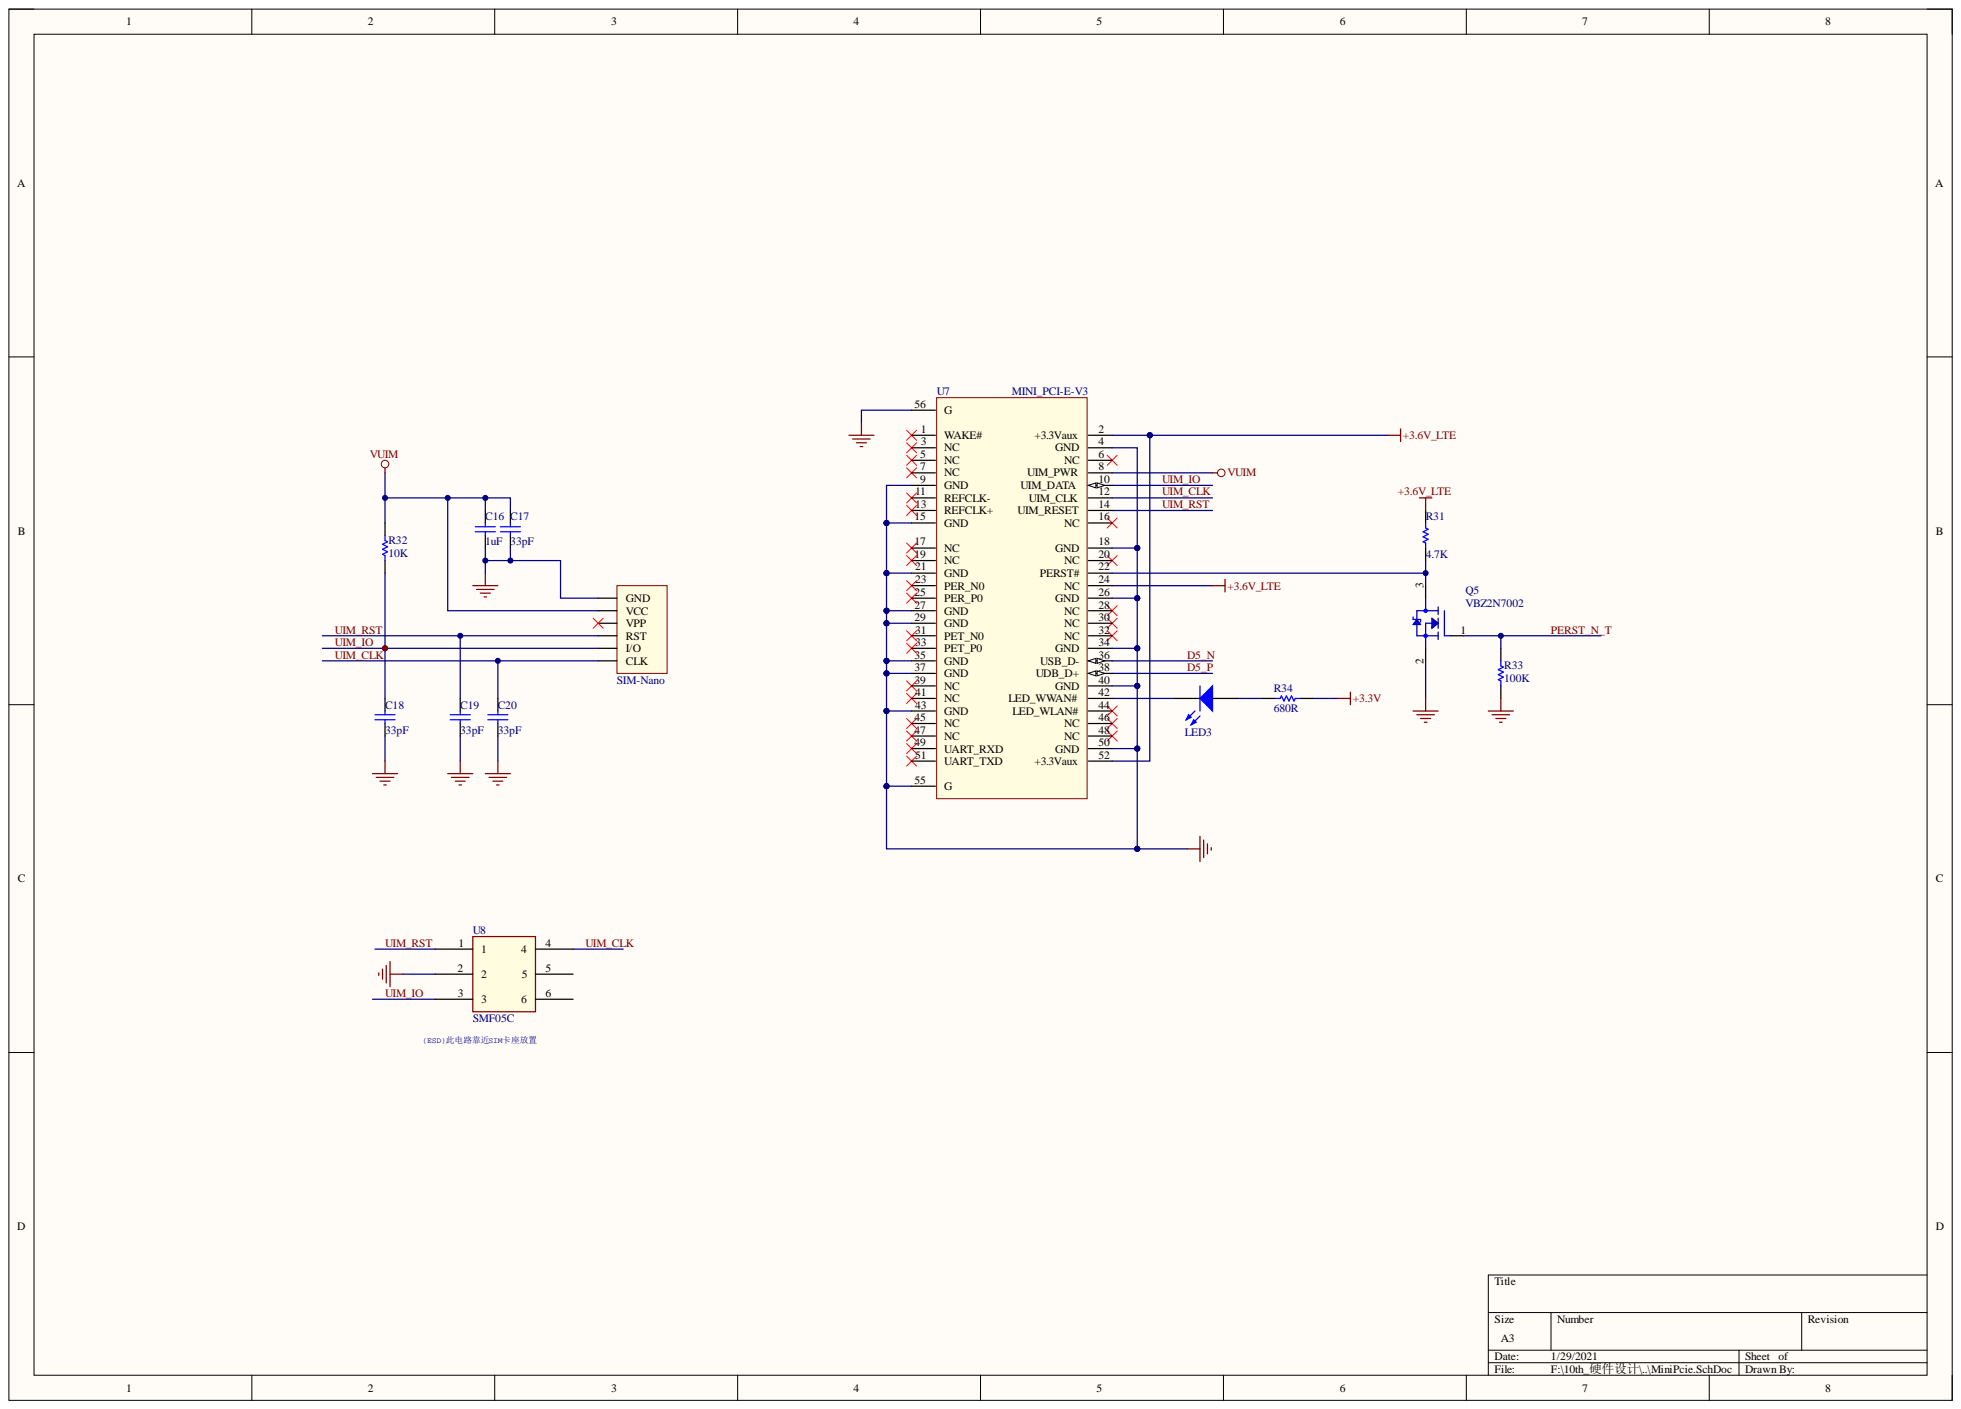
[picture p85: page 3]

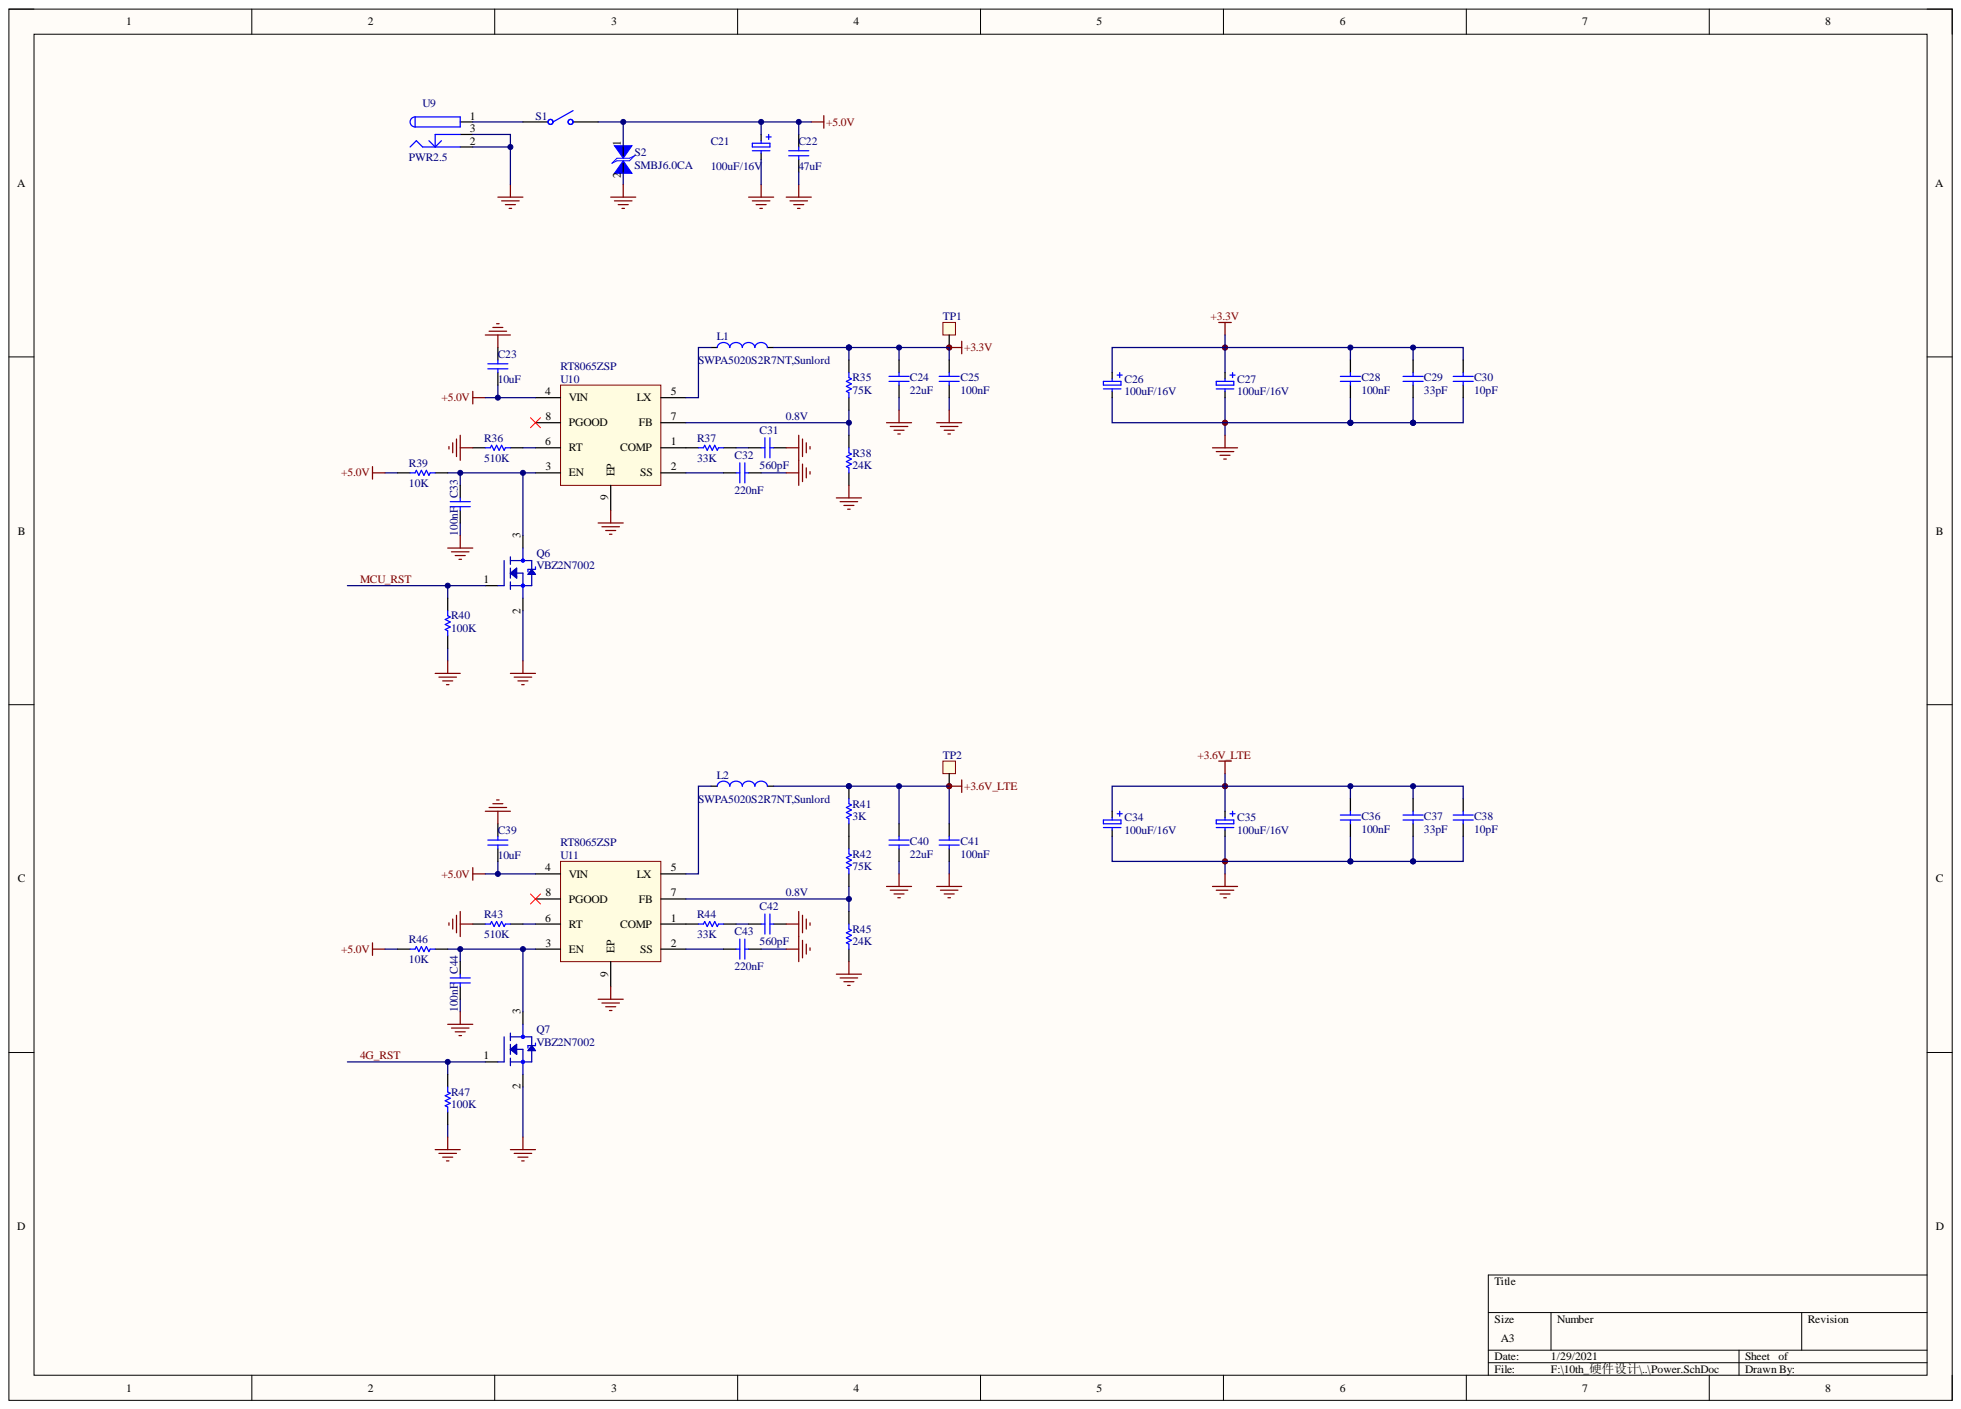
[picture p86: page 4]

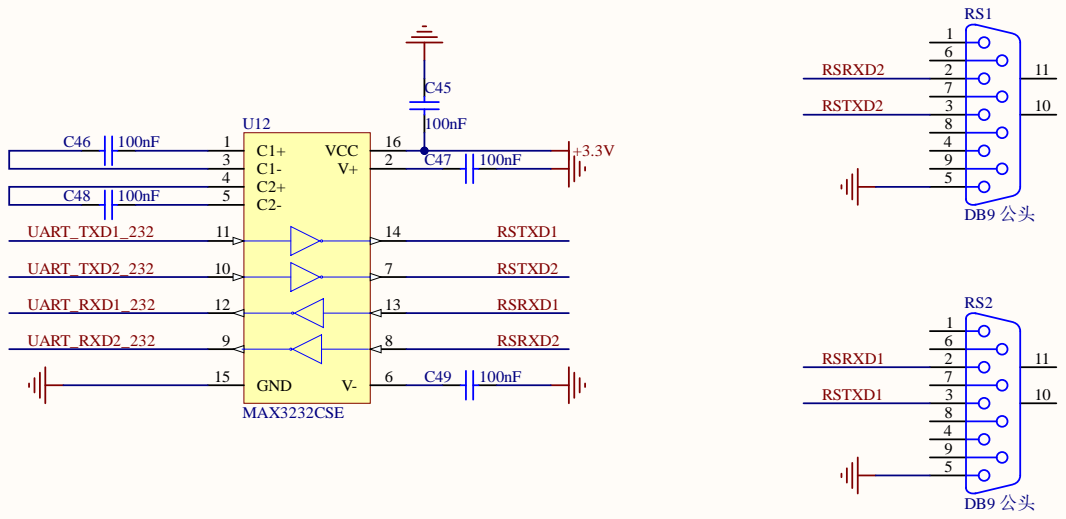
[picture p87: page 5]

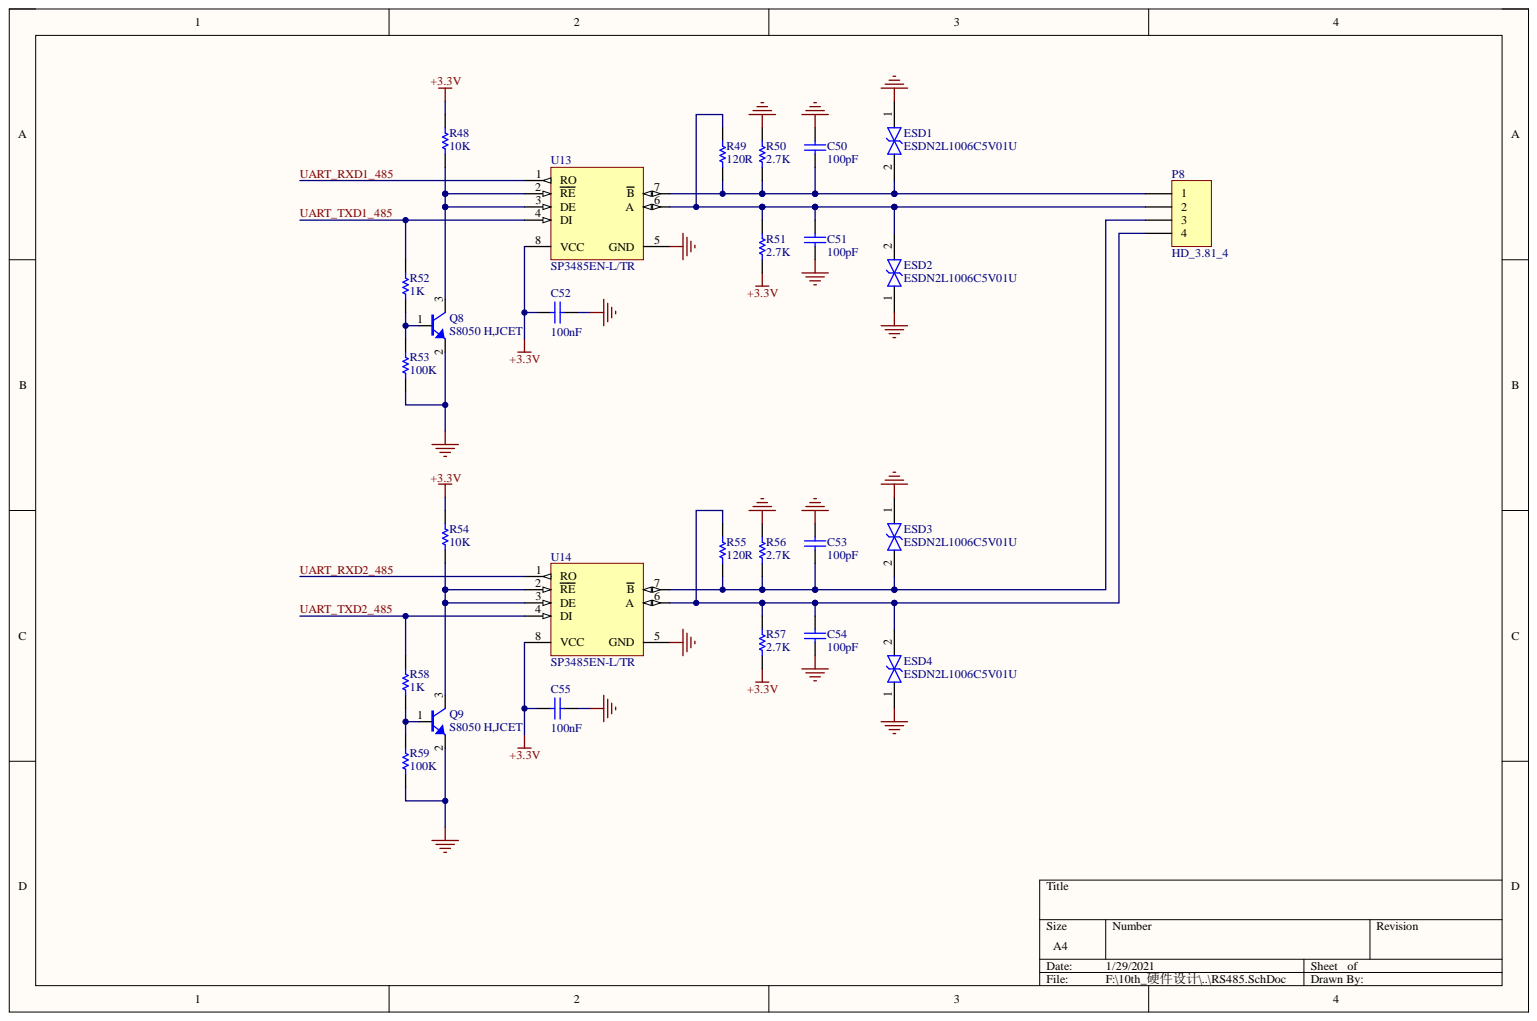
[picture p88: page 6]

4 8

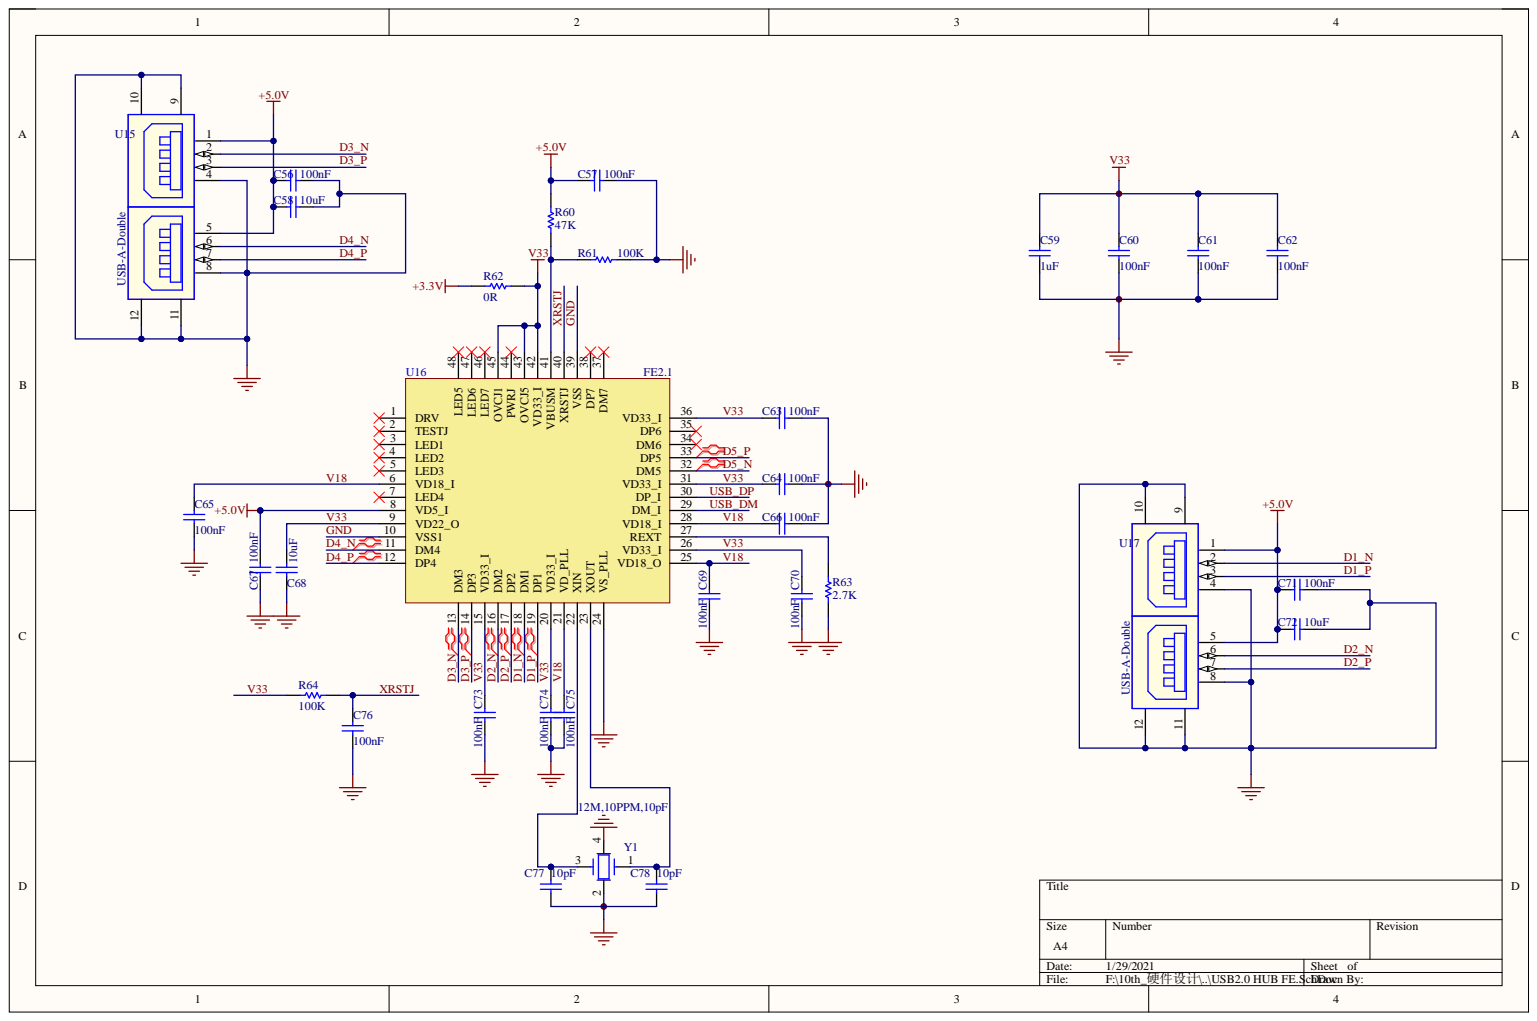
[picture p89: page 7]

M7 37 DP7 38 VSS 39 XRSTJ 40 VBUSM 41 VD33_I 42 OVCJ5 43 PWRJ 44 OVCJ1 45 LED7 46 LED6 47 LED5 48

7 | USB_ D M | 0 n F

2 | V 3 3
2 5 | V 1 8

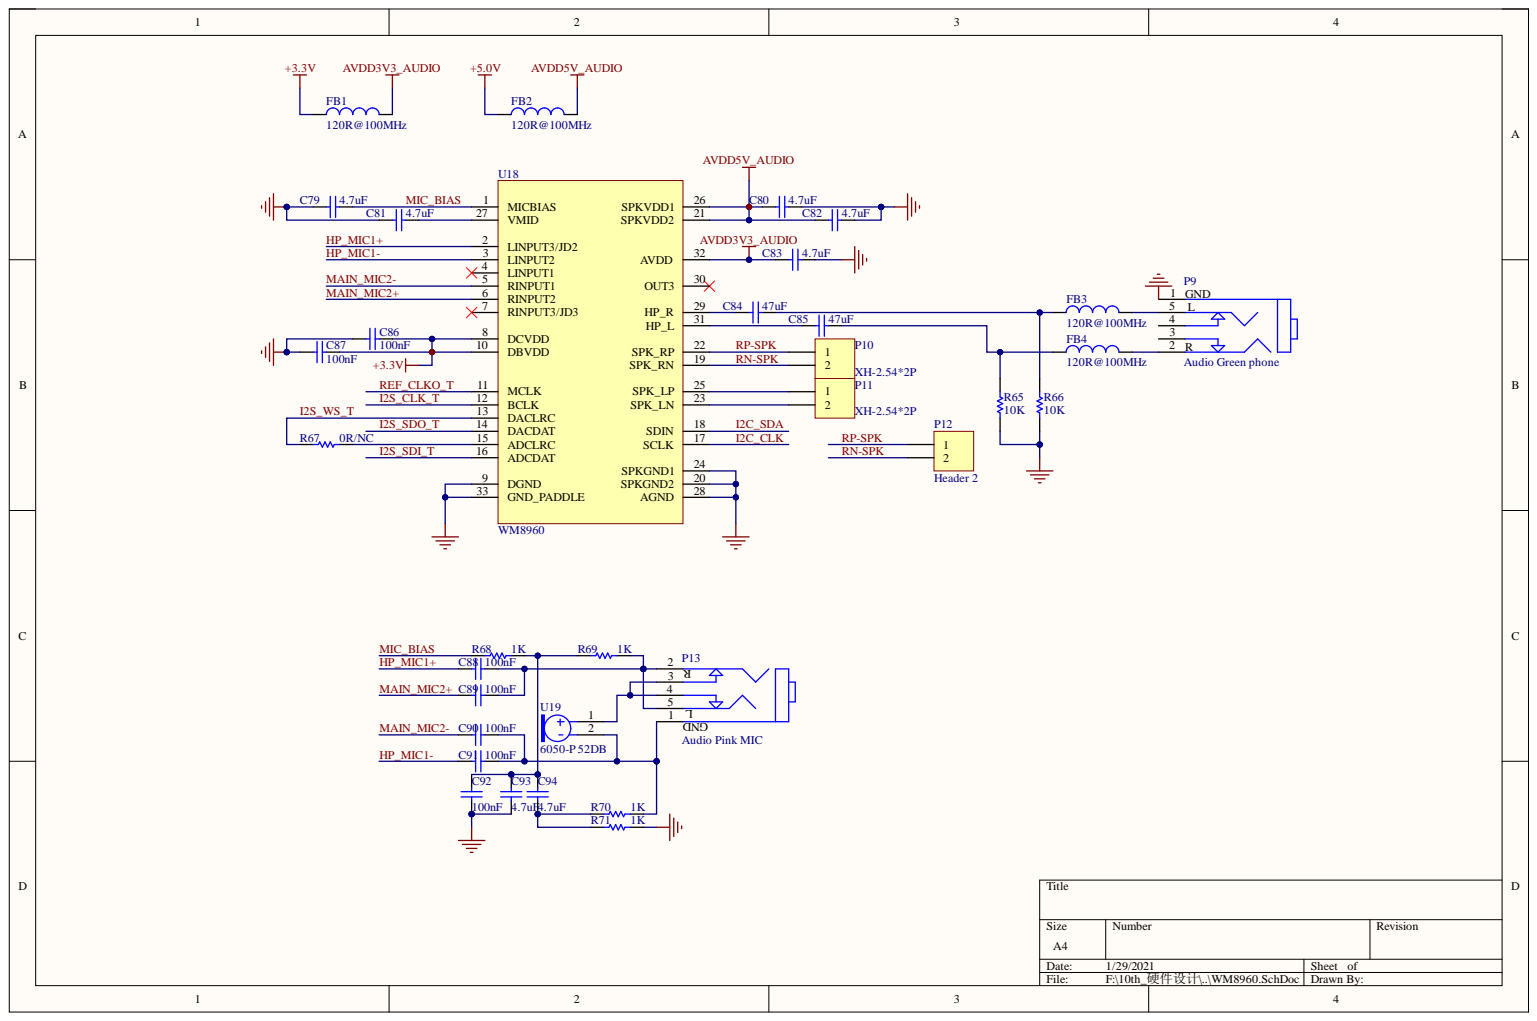
[picture p90: page 8]
