OpenHisiIpCam/camera-debug-facility/board/l107/l107-demo-board.pdf

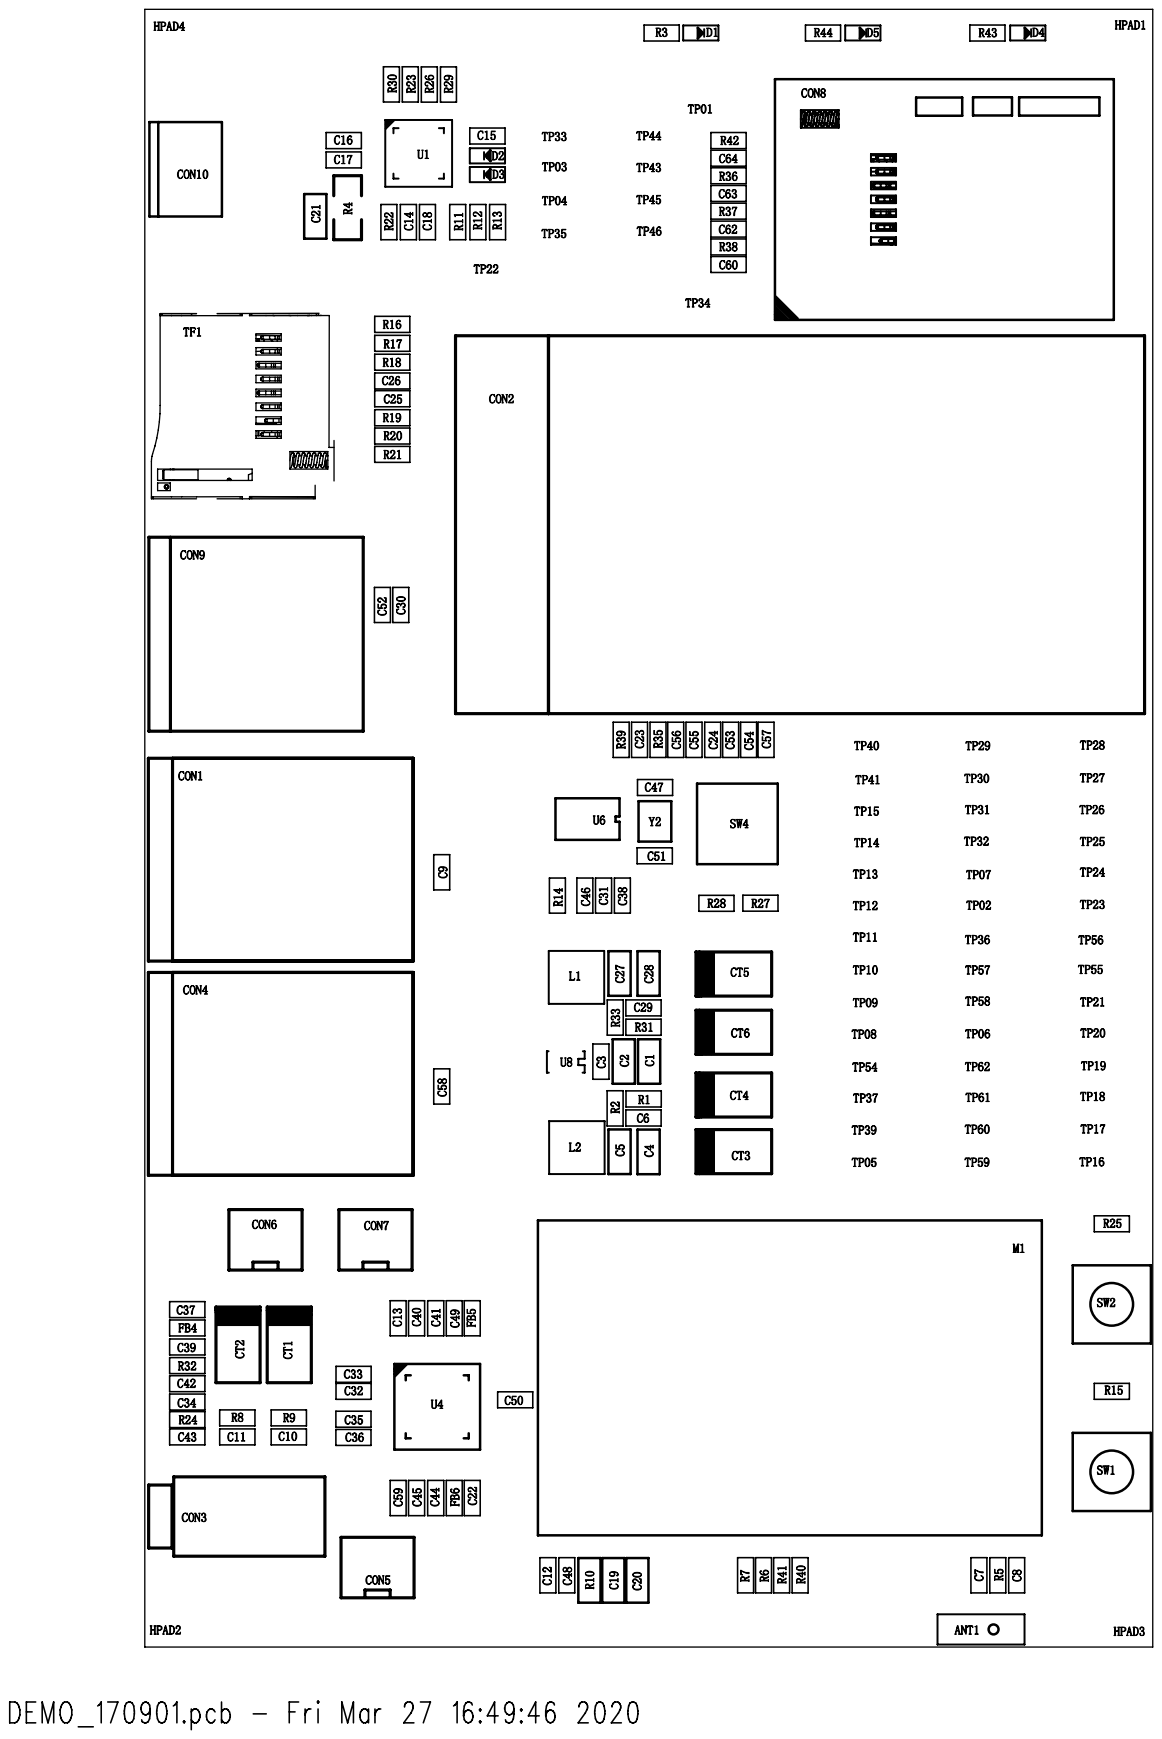
[picture p96: page 1]
