OpenHisiIpCam/camera-debug-facility/hardware/cdf-2/cdf-2.kicad_pcb

## KiCad design schematics/acia_isolation.kicad_sch

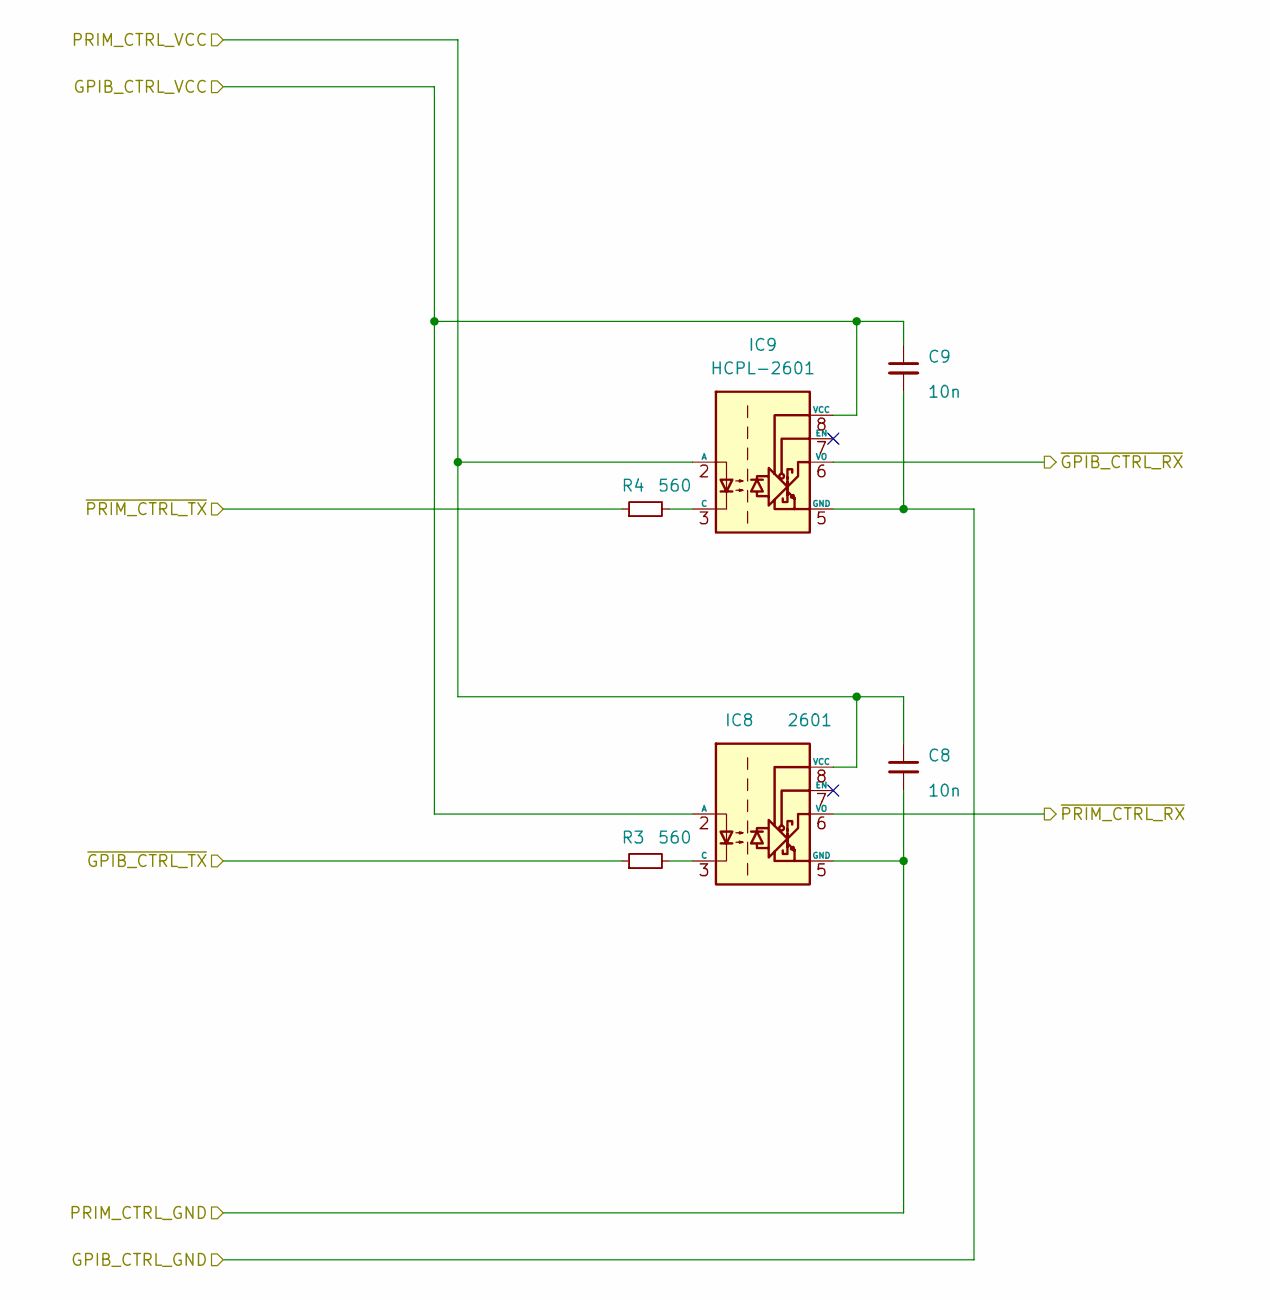
[picture p97: schematic acia_isolation.kicad_sch]

Parts:
C8, C9: 10n
IC8: 2601; DIP-8_W7.62mm
IC9: HCPL-2601; DIP-8_W7.62mm
R3, R4: 560

Connections:
GPIB_CTRL_GND: C9.2, IC9.5 (GND)
GPIB_CTRL_VCC: C9.1, IC8.2 (A), IC9.8 (VCC)
unnamed: IC8.3 (C), R3.2
unnamed: IC9.3 (C), R4.2
PRIM_CTRL_GND: C8.2, IC8.5 (GND)
PRIM_CTRL_VCC: C8.1, IC8.8 (VCC), IC9.2 (A)
~GPIB_CTRL_RX: IC9.6 (VO)
~GPIB_CTRL_TX: R3.1
~PRIM_CTRL_RX: IC8.6 (VO)
~PRIM_CTRL_TX: R4.1
