OpenHisiIpCam/camera-debug-facility/hardware/cdf-2/cdf-2.kicad_pcb

## KiCad design schematics/buck_conv_pos.kicad_sch

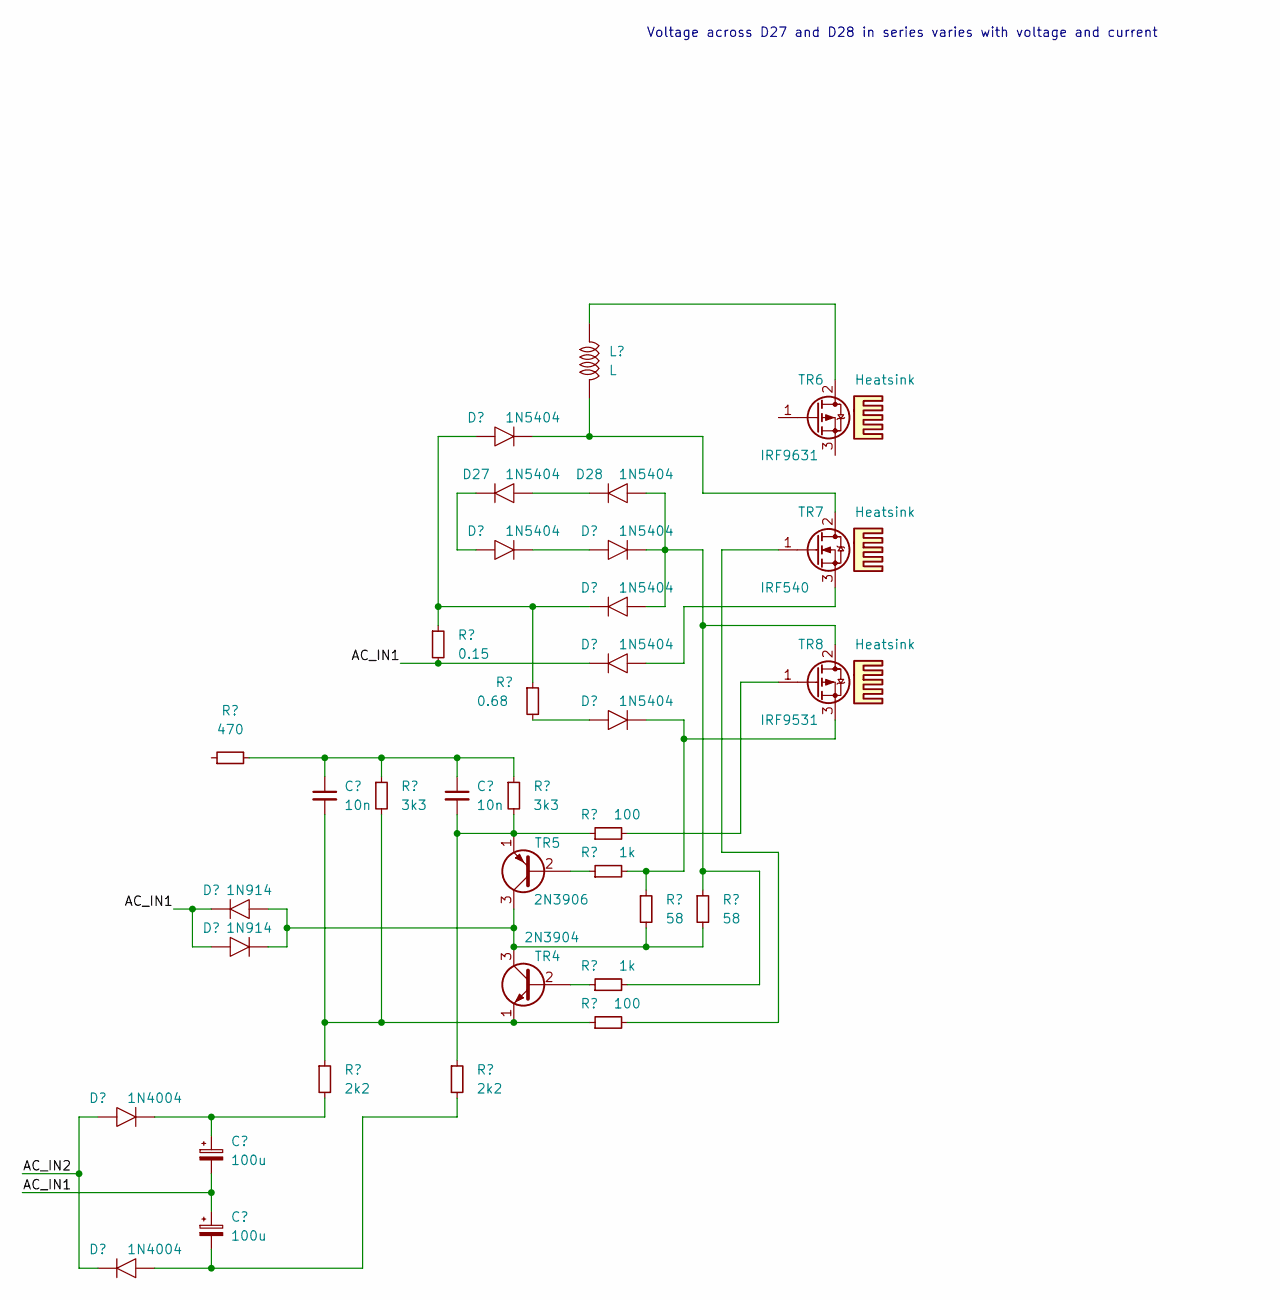
[picture p98: schematic buck_conv_pos.kicad_sch]

Parts:
D27, D28: 1N5404; D_DO-201AD_P15.24mm_Horizontal
TR4: 2N3904; TO-92_Inline
TR5: 2N3906; TO-92_Inline
TR6: IRF9631
TR7: IRF540
TR8: IRF9531

Connections:
unnamed: D27., D28.
unnamed: D28., TR8.2
unnamed: TR4.3 (C), TR5.3 (C)

Notes on the sheet:
Voltage across D27 and D28 in series varies with voltage and current
