OpenHisiIpCam/camera-debug-facility/hardware/cdf-2/cdf-2.kicad_pcb

## KiCad design schematics/primary_processor.kicad_sch

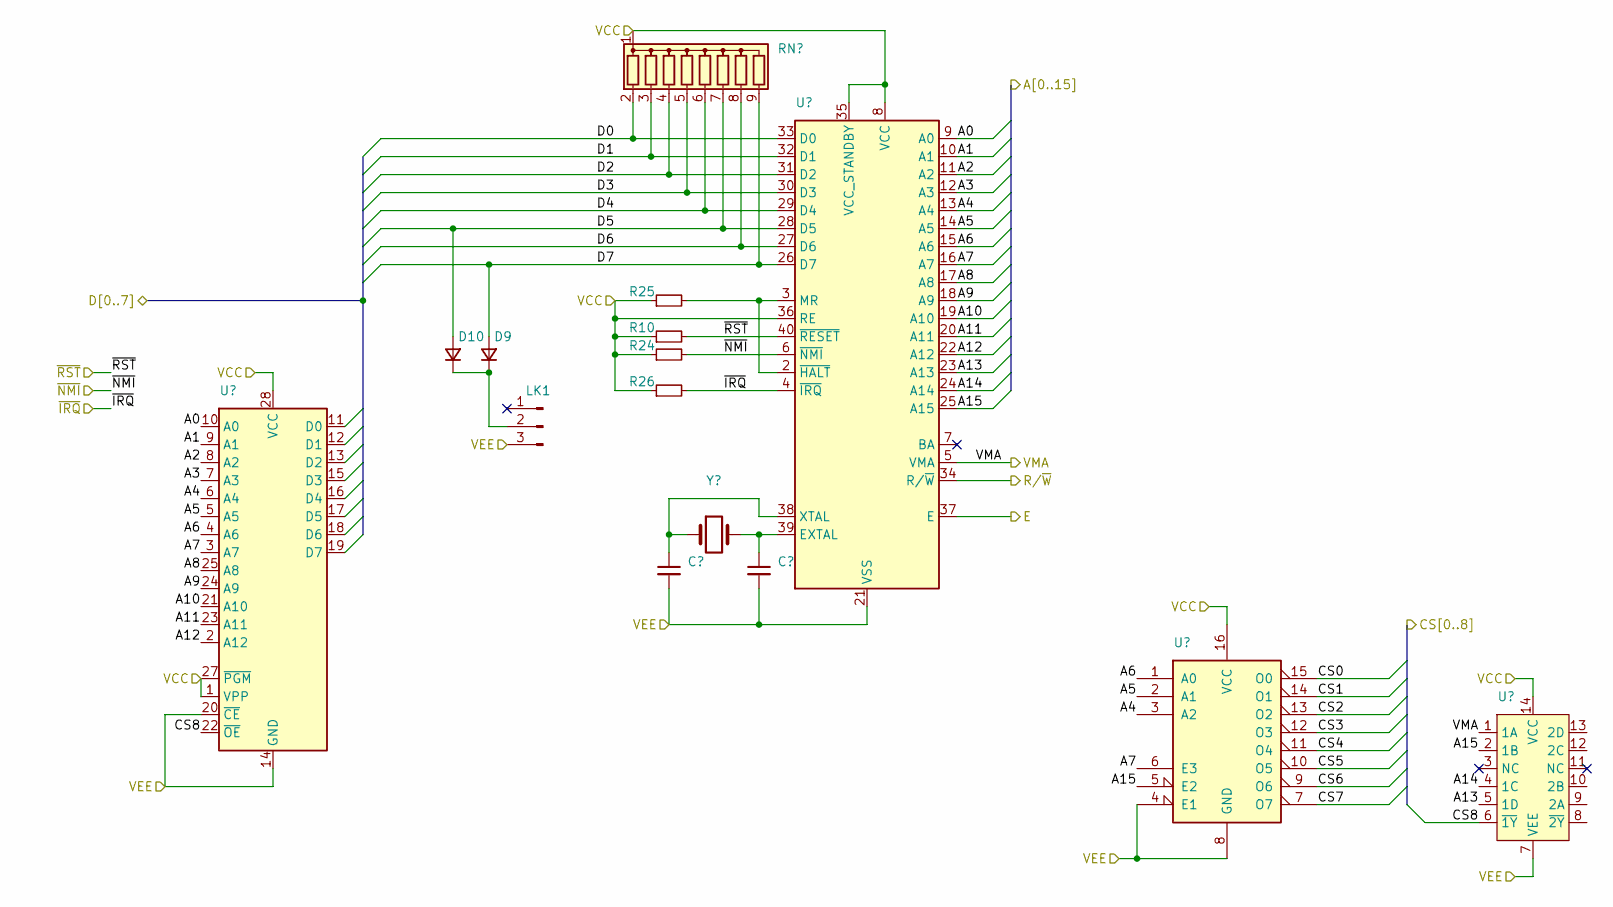
[picture p100: schematic primary_processor.kicad_sch]

Parts:
D9, D10: (no value)
LK1: (no value)
R10, R24, R25, R26: (no value)

Connections:
D5: D10.2 (A)
D7: D9.2 (A)
unnamed: D9.1 (K), D10.1 (K), LK1.2
VCC: R10.1, R24.1, R25.1, R26.1
VEE: LK1.3
~IRQ: R26.2
~NMI: R24.2
~RST: R10.2
